theatrus/ledbrick/firmware/components/ledbrick_scheduler/ledbrick_scheduler.cpp

#include "ledbrick_scheduler.h"
#include "cJSON.h"
#include "esphome/core/log.h"
#include "esphome/core/application.h"
#include "esphome/components/light/light_state.h"
#include "esphome/components/number/number.h"
#include <algorithm>
#include <cmath>
#include <cstdlib>
#include <memory>

// The standalone implementations are compiled separately by ESPHome
// No need to include the .cpp files here

namespace esphome {
namespace ledbrick_scheduler {

static const char *const TAG = "ledbrick_scheduler";

void LEDBrickScheduler::setup() {
  ESP_LOGCONFIG(TAG, "Setting up LEDBrick Scheduler...");
  
  // Initialize the standalone scheduler
  scheduler_.set_num_channels(num_channels_);
  
  // Initialize the astronomical calculator with default location
  astro_calc_.set_location(latitude_, longitude_);
  astro_calc_.set_projection_settings(astronomical_projection_, time_shift_hours_, time_shift_minutes_);
  
  // Initialize persistent storage
  schedule_pref_ = global_preferences->make_preference<ScheduleStorage>(SCHEDULE_HASH);
  led_models_pref_ = global_preferences->make_preference<LedModelsStorage>(LED_MODELS_HASH);
  emergency_pref_ = global_preferences->make_preference<bool>(EMERGENCY_HASH);
  
  // Set up temperature hardware callbacks (moved from controller to hardware manager)
  temp_hardware_.set_fan_pwm_callback([this](float pwm) { this->on_fan_pwm_change(pwm); });
  temp_hardware_.set_fan_enable_callback([this](bool enabled) { this->on_fan_enable_change(enabled); });
  temp_hardware_.set_emergency_callback([this](bool emergency) { this->on_emergency_change(emergency); });
  
  // A thermal emergency survives a restart: keep the LEDs off until a reading confirms recovery.
  // Restore it before the schedule loads, so nothing turns the outputs on first.
  bool saved_emergency = false;
  if (emergency_pref_.load(&saved_emergency) && saved_emergency) {
    ESP_LOGW(TAG, "Thermal emergency was active before restart; LEDs stay off until temperatures recover");
    // Only the latch here: the fan component is not set up yet, so the first update()
    // sends the full-speed fan command once it can take effect
    ledbrick::TemperatureControlCommand command;
    command.emergency_state = true;
    command.override_normal_control = true;
    command.reason = "Thermal emergency restored after restart";
    temp_hardware_.apply_command(command, millis());
    temp_control_.update_hardware_state(temp_hardware_.get_hardware_state());
  }
  
  // Load schedule from flash storage (includes all settings in JSON). The custom LED
  // models come first, since channels name them.
  load_led_models_from_flash();
  load_schedule_from_flash();
  std::string model_error;
  if (!scheduler_.channels_have_models(&model_error)) {
    ESP_LOGE(TAG, "%s; using the standard LED for it until the model is posted to /api/led_models",
             model_error.c_str());
  }
  
  // Initialize temperature control
  temp_control_.set_config(temp_config_);
  
  // Enable temperature control unless the enable switch already restored a setting
  if (!temp_control_enable_requested_) {
    temp_control_.enable(true);
  }
  temp_control_initialized_ = true;
  
  // Try to get initial timezone from time source
  if (time_source_) {
    auto time = time_source_->now();
    if (time.is_valid()) {
      double detected_offset = static_cast<double>(time.timezone_offset()) / 3600.0;
      if (abs(detected_offset - timezone_offset_hours_) > 0.01) {
        ESP_LOGI(TAG, "Initial timezone offset detected: %.1fh (was %.1fh)", 
                 detected_offset, timezone_offset_hours_);
        timezone_offset_hours_ = detected_offset;
        astro_calc_.set_timezone_offset(timezone_offset_hours_);
      }
    }
  }
  
  // Load default astronomical schedule if no points exist
  if (scheduler_.is_schedule_empty()) {
    load_preset("default");
    if (flash_load_failed_) {
      // Run the default preset, but leave the saved copy alone rather than overwrite it at boot
      ESP_LOGE(TAG, "Saved schedule could not be loaded; running the default preset without saving it");
      save_pending_ = false;
    } else {
      ESP_LOGI(TAG, "No saved schedule found, loaded default preset");
      save_schedule_to_flash();  // Save the default schedule
    }
  }
  
  ESP_LOGI(TAG, "Schedule loaded - %zu points, %u channels, enabled: %s", 
           scheduler_.get_schedule_size(), num_channels_, enabled_ ? "true" : "false");
  
  // Update color sensors with initial values
  update_color_sensors();
  
  ESP_LOGCONFIG(TAG, "LEDBrick Scheduler setup complete");
  ESP_LOGCONFIG(TAG, "Temperature Control:");
  ESP_LOGCONFIG(TAG, "  Fan object: %s", fan_ ? "Connected" : "NOT CONNECTED");
  ESP_LOGCONFIG(TAG, "  Fan power switch: %s", fan_power_switch_ ? "Connected" : "NOT CONNECTED");
  ESP_LOGCONFIG(TAG, "  Temperature sensors: %zu", temp_sensors_.size());
  
  // Mark boot as complete and perform any deferred saves
  boot_complete_ = true;
  if (save_pending_) {
    ESP_LOGI(TAG, "Boot complete - performing deferred schedule save");
    save_pending_ = false;
    save_schedule_to_flash();
  }
}

void LEDBrickScheduler::update() {
  // ALWAYS check thermal emergency first, even if scheduler is disabled
  if (temp_hardware_.get_hardware_state().thermal_emergency) {
    // During thermal emergency, continuously force all outputs to zero
    // This prevents manual control from setting unsafe values
    for (uint8_t channel = 0; channel < num_channels_; channel++) {
      force_channel_output(channel, 0.0f, 0.0f);
    }
    // Skip to temperature control update
  } else if (!enabled_) {
    ESP_LOGV(TAG, "Scheduler disabled, skipping schedule update");
    // When scheduler is disabled but not in emergency, we don't change outputs
    // This allows manual control to work
  } else if (!has_valid_time()) {
    // Hold the outputs until the clock is set; the 00:00 values would be wrong
    uint32_t now = millis();
    if (last_time_warning_ms_ == 0 || now - last_time_warning_ms_ > 60000) {
      ESP_LOGW(TAG, "No valid time yet, holding channel outputs");
      last_time_warning_ms_ = now == 0 ? 1 : now;
    }
  } else {
    // Normal scheduler operation
    // Update timezone offset from time source if available
    update_timezone_from_time_source();
    
    // Update astronomical times for dynamic schedule points
    update_astronomical_times_for_scheduler();
    
    // Get current values from standalone scheduler and apply them. Interpolate to the
    // second so ramps move at every update instead of in one-minute steps
    uint16_t current_time = get_current_time_minutes();
    
    // Use astronomical interpolation if we have dynamic points
    auto values = scheduler_.get_values_at_seconds_with_astro(get_current_time_seconds(), scheduler_.get_astronomical_times());
    ESP_LOGD(TAG, "Scheduler values at %02d:%02d - valid: %s, channels: %zu, schedule_points: %zu", 
             current_time / 60, current_time % 60, 
             values.valid ? "true" : "false", 
             values.pwm_values.size(),
             scheduler_.get_schedule_size());
             
    // Check if moon simulation is active
    if (scheduler_.get_moon_simulation().enabled && values.valid && values.pwm_values.size() > 0) {
      // Get moon visibility status
      auto moon_times = get_moon_rise_set_times();
      bool moon_visible = (moon_times.rise_minutes < moon_times.set_minutes) ?
                         (current_time >= moon_times.rise_minutes && current_time <= moon_times.set_minutes) :
                         (current_time >= moon_times.rise_minutes || current_time <= moon_times.set_minutes);
      
      // Check if channels are dark
      bool all_dark = true;
      for (size_t i = 0; i < values.pwm_values.size(); i++) {
        if (values.pwm_values[i] > 0.1f) {
          all_dark = false;
          break;
        }
      }
      
      ESP_LOGD(TAG, "Moon sim status - Enabled: yes, Moon visible: %s, Channels dark: %s, Phase: %.1f%%, Ch1: PWM=%.1f%%, Current=%.3fA", 
               moon_visible ? "yes" : "no",
               all_dark ? "yes" : "no",
               get_moon_phase() * 100.0f,
               values.pwm_values[0], values.current_values[0]);
    }
    
    if (values.valid) {
      apply_values(values);
    } else {
      ESP_LOGW(TAG, "Scheduler returned invalid values at time %02d:%02d, schedule has %zu points", 
               current_time / 60, current_time % 60, scheduler_.get_schedule_size());
    }
  }
  
  // Update temperature control
  uint32_t current_millis = millis();
  if (temp_control_initialized_ && current_millis - last_temp_update_ >= 1000) {  // Update every second
    last_temp_update_ = current_millis;
    
    // Update temperature sensors
    update_temperature_sensors();
    
    // Update fan speed
    update_fan_speed();
    
    // Run temperature control update with new command-based interface
    auto command = temp_control_.compute_control_command(current_millis);
    temp_hardware_.apply_command(command, current_millis);
    temp_control_.update_hardware_state(temp_hardware_.get_hardware_state());
    
    // Publish sensor values periodically (every 5 seconds)
    if (current_millis - last_sensor_publish_ >= 5000) {
      publish_temp_sensor_values();
      last_sensor_publish_ = current_millis;
    }
  }
  
  // Log status every 10 seconds (reduce log spam)
  if (current_millis - last_log_time_ms_ > 10000) {
    if (temp_hardware_.get_hardware_state().thermal_emergency) {
      ESP_LOGD(TAG, "THERMAL EMERGENCY - All outputs forced to zero");
    } else if (!enabled_) {
      ESP_LOGD(TAG, "Scheduler disabled - manual control active");
    } else {
      uint16_t log_time = get_current_time_minutes();
      auto log_values = scheduler_.get_values_at_time_with_astro(log_time, scheduler_.get_astronomical_times());
      ESP_LOGD(TAG, "Scheduler active at %02u:%02u - Ch1: PWM=%.1f%%, Ch2: PWM=%.1f%%, Moon: %s", 
               log_time / 60, log_time % 60,
               log_values.pwm_values.size() > 0 ? log_values.pwm_values[0] : 0.0f,
               log_values.pwm_values.size() > 1 ? log_values.pwm_values[1] : 0.0f,
               scheduler_.get_moon_simulation().enabled ? "enabled" : "disabled");
      
      // Also log if we recently recovered from emergency
      bool current_emergency = temp_hardware_.get_hardware_state().thermal_emergency;
      if (was_emergency_ && !current_emergency) {
        recovery_time_ms_ = current_millis;
        ESP_LOGI(TAG, "Recently recovered from thermal emergency");
      }
      if (recovery_time_ms_ > 0 && current_millis - recovery_time_ms_ < 30000) {  // Log for 30 seconds after recovery
        ESP_LOGD(TAG, "Post-emergency recovery: %" PRIu32 " seconds ago", (current_millis - recovery_time_ms_) / 1000);
      }
      was_emergency_ = current_emergency;
    }
    last_log_time_ms_ = current_millis;
  }
}

void LEDBrickScheduler::dump_config() {
  ESP_LOGCONFIG(TAG, "LEDBrick Scheduler:");
  ESP_LOGCONFIG(TAG, "  Channels: %u", num_channels_);
  ESP_LOGCONFIG(TAG, "  Update Interval: %" PRIu32 " ms", this->get_update_interval());
  ESP_LOGCONFIG(TAG, "  Enabled: %s", enabled_ ? "YES" : "NO");
  ESP_LOGCONFIG(TAG, "  PWM Scale: %.2f (%.0f%%)", pwm_scale_, pwm_scale_ * 100.0f);
  ESP_LOGCONFIG(TAG, "  Timezone: %s (UTC%+.1fh)", timezone_.c_str(), timezone_offset_hours_);
  ESP_LOGCONFIG(TAG, "  Location: %.4f°N, %.4f°W", latitude_, -longitude_);
  ESP_LOGCONFIG(TAG, "  Schedule Points: %zu", scheduler_.get_schedule_size());
  ESP_LOGCONFIG(TAG, "  Time Source: %s", time_source_ ? "CONFIGURED" : "NOT SET");
  
  if (astronomical_projection_) {
    ESP_LOGCONFIG(TAG, "  Astronomical Projection: ENABLED");
    ESP_LOGCONFIG(TAG, "  Time Shift: %+dh %+dm", time_shift_hours_, time_shift_minutes_);
  } else {
    ESP_LOGCONFIG(TAG, "  Astronomical Projection: DISABLED");
  }
  
  if (time_source_) {
    uint16_t current_time = get_current_time_minutes();
    ESP_LOGCONFIG(TAG, "  Current Local Time: %02u:%02u (%u minutes)", 
                  current_time / 60, current_time % 60, current_time);
  }
  
  // Temperature control configuration
  ESP_LOGCONFIG(TAG, "Temperature Control:");
  ESP_LOGCONFIG(TAG, "  Target Temperature: %.1f°C", temp_config_.target_temp_c);
  ESP_LOGCONFIG(TAG, "  PID Parameters: Kp=%.2f, Ki=%.3f, Kd=%.2f", temp_config_.kp, temp_config_.ki, temp_config_.kd);
  ESP_LOGCONFIG(TAG, "  Fan PWM Range: %.1f%% - %.1f%%", temp_config_.min_fan_pwm, temp_config_.max_fan_pwm);
  ESP_LOGCONFIG(TAG, "  Emergency Temperature: %.1f°C", temp_config_.emergency_temp_c);
  ESP_LOGCONFIG(TAG, "  Temperature Sensors: %zu", temp_sensors_.size());
}

void LEDBrickScheduler::add_schedule_point(const SchedulePoint &point) {
  scheduler_.add_schedule_point(point);
  
  // Save to flash automatically
  save_schedule_to_flash();
  
  ESP_LOGD(TAG, "Added schedule point at %02u:%02u", 
           point.time_minutes / 60, point.time_minutes % 60);
}

void LEDBrickScheduler::set_schedule_point(uint16_t time_minutes, const std::vector<float> &pwm_values, 
                                          const std::vector<float> &current_values) {
  scheduler_.set_schedule_point(time_minutes, pwm_values, current_values);
  
  // Save to flash automatically
  save_schedule_to_flash();
}

void LEDBrickScheduler::add_dynamic_schedule_point(LEDScheduler::DynamicTimeType type, int16_t offset_minutes,
                                                  const std::vector<float> &pwm_values,
                                                  const std::vector<float> &current_values) {
  scheduler_.add_dynamic_schedule_point(type, offset_minutes, pwm_values, current_values);
  
  // Save to flash automatically
  save_schedule_to_flash();
  
  ESP_LOGD(TAG, "Added dynamic schedule point: %s %+d minutes", 
           LEDScheduler::dynamic_time_type_to_string(type).c_str(), offset_minutes);
}

void LEDBrickScheduler::remove_schedule_point(uint16_t time_minutes) {
  scheduler_.remove_schedule_point(time_minutes);
  
  // Save to flash automatically
  save_schedule_to_flash();
  
  ESP_LOGD(TAG, "Removed schedule point at %02u:%02u", time_minutes / 60, time_minutes % 60);
}

void LEDBrickScheduler::remove_dynamic_schedule_point(LEDScheduler::DynamicTimeType type, int16_t offset_minutes) {
  scheduler_.remove_dynamic_schedule_point(type, offset_minutes);
  
  // Save to flash automatically
  save_schedule_to_flash();
  
  ESP_LOGD(TAG, "Removed dynamic schedule point: %s %+d minutes", 
           LEDScheduler::dynamic_time_type_to_string(type).c_str(), offset_minutes);
}

void LEDBrickScheduler::clear_schedule() {
  scheduler_.clear_schedule();
  
  // Save to flash automatically
  save_schedule_to_flash();
  
  ESP_LOGD(TAG, "Cleared all schedule points");
}

bool LEDBrickScheduler::load_preset(const std::string &preset_name, bool save) {
  if (preset_name == "sunrise_sunset") {
    create_sunrise_sunset_preset_with_astro_data();
  } else if (!scheduler_.load_preset(preset_name)) {
    ESP_LOGW(TAG, "Unknown preset '%s'; schedule unchanged", preset_name.c_str());
    return false;
  }

  if (save) {
    save_schedule_to_flash();
  }

  ESP_LOGI(TAG, "Loaded preset '%s' with %zu points", preset_name.c_str(), scheduler_.get_schedule_size());
  return true;
}

void LEDBrickScheduler::save_preset(const std::string &preset_name) {
  scheduler_.save_preset(preset_name);
  ESP_LOGI(TAG, "Saved current schedule as preset '%s'", preset_name.c_str());
}

bool LEDBrickScheduler::has_valid_time() const {
  return time_source_ != nullptr && time_source_->now().is_valid();
}

uint16_t LEDBrickScheduler::get_current_time_minutes() const {
  if (!time_source_) {
    ESP_LOGW(TAG, "No time source configured");
    return 0;
  }
  
  auto time = time_source_->now();
  if (!time.is_valid()) {
    ESP_LOGW(TAG, "Time source not available");
    return 0;
  }
  
  return time.hour * 60 + time.minute;
}

uint32_t LEDBrickScheduler::get_current_time_seconds() const {
  if (!time_source_) {
    return 0;
  }
  auto time = time_source_->now();
  if (!time.is_valid()) {
    return 0;
  }
  return time.hour * 3600u + time.minute * 60u + time.second;
}

InterpolationResult LEDBrickScheduler::get_current_values() const {
  // Same interpolation as update(), so dynamic (sunrise-relative etc.) points count
  return scheduler_.get_values_at_seconds_with_astro(get_current_time_seconds(), scheduler_.get_astronomical_times());
}

float LEDBrickScheduler::get_led_temperature_c() const {
  // The emitter's sensors sit on the board near the LEDs' pads. Without a working one,
  // use the reference temperature, which leaves the output uncompensated.
  const auto &status = temp_control_.get_status();
  if (status.sensors_valid_count > 0 && std::isfinite(status.current_temp_c) && status.current_temp_c > 0.0f) {
    return status.current_temp_c;
  }
  return 25.0f;
}

float LEDBrickScheduler::get_channel_level(uint8_t channel) const {
  if (!scheduler_.is_curve_channel(channel) || channel >= last_levels_.size()) {
    return -1.0f;
  }
  return last_levels_[channel];
}

bool LEDBrickScheduler::set_channel_dimming(uint8_t channel, ledbrick::DimMode mode, ledbrick::DimPriority priority,
                                            float floor_current, const std::vector<ledbrick::LedGroup> &leds,
                                            std::string *error) {
  if (!scheduler_.set_channel_dimming(channel, mode, priority, floor_current, leds, error)) {
    return false;
  }
  ESP_LOGI(TAG, "Channel %u dimming: %s, %s first, floor %.3f A, %s LEDs", channel + 1,
           mode == ledbrick::DimMode::CURVE ? "curve" : "manual",
           priority == ledbrick::DimPriority::PWM_FIRST ? "PWM" : "current", floor_current,
           leds.empty() ? "default" : "custom");
  // Drive the channel the new way at the next update, without a transition
  force_next_update_ = true;
  return true;
}

bool LEDBrickScheduler::set_led_models_json(const std::string &json, std::string *error, bool *save_failed) {
  *save_failed = false;
  // A set too large for its record is refused before anything changes
  if (!scheduler_.import_led_models_json(json, error, sizeof(LedModelsStorage::json_data) - 1)) {
    return false;
  }
  ESP_LOGI(TAG, "Custom LED models: %zu", scheduler_.get_custom_led_models().size());
  // Curve channels pick up the new curves at the next update
  force_next_update_ = true;
  if (!save_led_models_to_flash()) {
    if (error) *error = "LED models applied but not saved; they will be lost on restart";
    *save_failed = true;
    return false;
  }
  return true;
}

bool LEDBrickScheduler::set_channel_manual_level(uint8_t channel, float level) {
  if (!scheduler_.is_curve_channel(channel)) {
    ESP_LOGW(TAG, "Manual level rejected - channel %u is not in curve mode", channel);
    return false;
  }
  level = std::max(0.0f, std::min(level, 1.0f));
  ledbrick::DriveLimits limits;
  limits.max_current_a = scheduler_.get_channel_max_current(channel);
  ledbrick::Drive drive = scheduler_.channel_dimmer(channel).drive_for_level(level, limits, get_led_temperature_c());
  if (!set_channel_manual_control(channel, drive.pwm * 100.0f, drive.current_a)) {
    return false;
  }
  if (last_levels_.size() != num_channels_) {
    last_levels_.assign(num_channels_, -1.0f);
  }
  last_levels_[channel] = level;
  return true;
}

InterpolationResult LEDBrickScheduler::get_actual_channel_values() const {
  InterpolationResult result;
  result.pwm_values.resize(num_channels_, 0.0f);
  result.current_values.resize(num_channels_, 0.0f);
  result.valid = true;
  
  // Get actual values from the ESPHome components
  for (uint8_t channel = 0; channel < num_channels_; channel++) {
    // Get PWM value from light entity
    auto light_it = lights_.find(channel);
    if (light_it != lights_.end() && light_it->second) {
      // Get actual current state (not the call values)
      auto remote_values = light_it->second->remote_values;
      // Check if light is on - if off, report 0% regardless of brightness setting
      if (remote_values.is_on()) {
        // Get brightness as percentage (0-100)
        result.pwm_values[channel] = remote_values.get_brightness() * 100.0f;
      } else {
        // Light is off, report 0%
        result.pwm_values[channel] = 0.0f;
      }
    }
    
    // Get current value from current control
    auto current_it = current_controls_.find(channel);
    if (current_it != current_controls_.end() && current_it->second) {
      result.current_values[channel] = current_it->second->state;
    }
  }
  
  return result;
}

void LEDBrickScheduler::set_enabled(bool enabled) {
  if (enabled_ == enabled) {
    return;  // No change, skip save
  }

  enabled_ = enabled;

  // The scheduler's flash JSON is the only persisted copy of this setting
  save_schedule_to_flash();
  ESP_LOGI(TAG, "Scheduler %s and saved", enabled ? "enabled" : "disabled");
}

bool LEDBrickScheduler::set_pwm_scale(float scale) {
  if (scale < 0.0f) {
    scale = 0.0f;
  } else if (scale > 1.0f) {
    scale = 1.0f;
  }

  bool saved = true;
  if (abs(pwm_scale_ - scale) > 0.001f) {
    pwm_scale_ = scale;
    ESP_LOGI(TAG, "PWM scale set to %.2f (%.0f%%)", pwm_scale_, pwm_scale_ * 100.0f);
    saved = save_schedule_to_flash();

    // Force immediate update to apply new scale
    update();
  }
  return saved;
}

void LEDBrickScheduler::create_sunrise_sunset_preset_with_astro_data() const {
  // Calculate actual sunrise and sunset times using astronomical calculator
  update_astro_calculator_settings();
  auto dt = esphome_time_to_datetime();
  auto sun_times = astro_calc_.get_projected_sun_rise_set_times(dt);
  
  // Use calculated times or fallback to defaults
  uint16_t sunrise_minutes = sun_times.rise_valid ? sun_times.rise_minutes : 420;  // Default 7:00 AM
  uint16_t sunset_minutes = sun_times.set_valid ? sun_times.set_minutes : 1080;    // Default 6:00 PM
  
  ESP_LOGI(TAG, "Creating astronomical sunrise/sunset preset: sunrise=%02u:%02u, sunset=%02u:%02u", 
           sunrise_minutes / 60, sunrise_minutes % 60,
           sunset_minutes / 60, sunset_minutes % 60);
  
  // Use the standalone scheduler to create the default astronomical preset
  // Note: The new default preset is dynamic and doesn't use specific sunrise/sunset times
  const_cast<LEDScheduler&>(scheduler_).create_default_astronomical_preset();
}

void LEDBrickScheduler::apply_values(const InterpolationResult &values) {
  ESP_LOGD(TAG, "apply_values called - num_channels: %u, values_size: %zu, first_pwm: %.1f%%", 
           num_channels_, values.pwm_values.size(), 
           values.pwm_values.empty() ? 0.0f : values.pwm_values[0]);
  
  const float led_temp = get_led_temperature_c();
  for (uint8_t channel = 0; channel < num_channels_; channel++) {
    if (channel >= values.pwm_values.size() || channel >= values.current_values.size()) {
      ESP_LOGW(TAG, "Schedule has %zu channels, expected %u", values.pwm_values.size(), num_channels_);
      break;
    }

    auto current_it = current_controls_.find(channel);
    auto max_current_it = max_current_controls_.find(channel);
    float max_current = scheduler_.get_channel_max_current(channel);
    if (max_current_it != max_current_controls_.end() && max_current_it->second) {
      max_current = max_current_it->second->state;
    }

    // Manual channels: the schedule sets the PWM and current. Curve channels: it sets a
    // level, and the channel's LED curves give the current and PWM for it at the LEDs'
    // temperature.
    float target_current;
    float brightness;
    uint32_t transition_ms = force_next_update_ ? 0 : 1000;
    const bool curve = scheduler_.is_curve_channel(channel);
    if (curve) {
      float level = std::max(0.0f, std::min(values.pwm_values[channel] * pwm_scale_ / 100.0f, 1.0f));
      ledbrick::DriveLimits limits;
      limits.max_current_a = max_current;
      ledbrick::Drive drive = scheduler_.channel_dimmer(channel).drive_for_level(level, limits, led_temp);
      target_current = drive.current_a;
      brightness = drive.pwm;
      if (last_levels_.size() != num_channels_) {
        last_levels_.assign(num_channels_, -1.0f);
      }
      last_levels_[channel] = level;
      // Current and PWM change together; a PWM transition would lag behind the current
      transition_ms = 0;
    } else {
      target_current = std::min(values.current_values[channel], max_current);
      brightness = values.pwm_values[channel] * pwm_scale_ / 100.0f;
      if (channel < last_levels_.size()) {
        last_levels_[channel] = -1.0f;
      }
    }

    // Apply current control with limiting
    // We need to do this before applying PWM to ensure LED controller enters the right state
    if (current_it != current_controls_.end() && current_it->second) {

      // Always update regardless of whether value has changed
      // Set the current control value
      current_it->second->publish_state(target_current);
      
      if (last_current_values_.size() <= channel) {
        last_current_values_.resize(num_channels_, -1.0f);
      }
      last_current_values_[channel] = target_current;
      
      // Enhanced logging for channel 1 when values change
      if (channel == 0) {
        ESP_LOGD(TAG, "Ch1 current update: %.3fA (input: %.3fA, max limit: %.3fA, was: %.3fA)", 
                 target_current, values.current_values[channel],
                 max_current_it != max_current_controls_.end() && max_current_it->second ? 
                 max_current_it->second->state : 999.0f,
                 last_current_values_.size() > channel ? last_current_values_[channel] : -1.0f);
      }
      
      ESP_LOGV(TAG, "Updated current %u to %.3fA (limited from %.3fA)", 
               channel, target_current, values.current_values[channel]);
    } else {
      ESP_LOGVV(TAG, "No current control found for channel %u", channel);
    }

    // Apply PWM to light entity
    auto light_it = lights_.find(channel);
    if (light_it != lights_.end() && light_it->second) {
      float scaled_pwm = brightness * 100.0f;

      // Always update regardless of whether value has changed
      ESP_LOGD(TAG, "Updating light %u: scaled_pwm=%.2f%%, brightness=%.3f (was %.3f)%s",
               channel, scaled_pwm, brightness,
               (last_pwm_values_.size() > channel) ? last_pwm_values_[channel] : -1.0f,
               curve ? " [curve]" : "");

      // Create light call to set brightness. Curve channels dim below 0.1% with PWM, so
      // any duty the dimmer gives turns them on.
      bool on = curve ? brightness > 0.0f : brightness > 0.001f;
      auto call = light_it->second->make_call();
      call.set_state(on);
      if (on) {
        call.set_brightness(brightness);
      }
      // Manual channels ease over 1 s; curve channels and forced updates change at once
      call.set_transition_length(transition_ms);
      call.perform();
      
      ESP_LOGV(TAG, "Light %u call performed", channel);
      
      if (last_pwm_values_.size() <= channel) {
        last_pwm_values_.resize(num_channels_, -1.0f);
      }
      last_pwm_values_[channel] = brightness;
      
      ESP_LOGV(TAG, "Updated light %u brightness to %.3f (%.1f%% * %.2f scale = %.1f%%)", 
               channel, brightness, values.pwm_values[channel], pwm_scale_, scaled_pwm);
    } else {
      ESP_LOGVV(TAG, "No light entity found for channel %u", channel);
    }
    
  }
  
  // Clear force update flag after applying all values
  if (force_next_update_) {
    ESP_LOGD(TAG, "Force update completed - clearing flag");
    force_next_update_ = false;
  }
}


void LEDBrickScheduler::add_light(uint8_t channel, light::LightState *light) {
  lights_[channel] = light;
  ESP_LOGD(TAG, "Added light entity for channel %u", channel);
}

void LEDBrickScheduler::add_current_control(uint8_t channel, number::Number *control) {
  current_controls_[channel] = control;
  ESP_LOGD(TAG, "Added current control for channel %u", channel);
}

void LEDBrickScheduler::add_max_current_control(uint8_t channel, number::Number *control) {
  max_current_controls_[channel] = control;
  ESP_LOGD(TAG, "Added max current control for channel %u", channel);
}



bool LEDBrickScheduler::save_schedule_to_flash() {
  // Prevent saving during boot to avoid race conditions
  if (!boot_complete_) {
    save_pending_ = true;
    ESP_LOGD(TAG, "Boot in progress - deferring schedule save");
    return true;
  }
  
  // Export the complete schedule as JSON (includes moon settings, channel configs, etc.)
  std::string json_output;
  export_schedule_json(json_output, true);
  
  // Allocate storage on heap to avoid stack overflow
  std::unique_ptr<ScheduleStorage> storage(new (std::nothrow) ScheduleStorage);
  if (!storage) {
    ESP_LOGE(TAG, "Failed to allocate memory for schedule storage");
    return false;
  }
  
  // A truncated document cannot be parsed at the next boot, so keep the previous copy instead
  if (json_output.length() >= sizeof(storage->json_data)) {
    ESP_LOGE(TAG, "Schedule JSON too large to save (%zu bytes, limit %zu); keeping previous copy",
             json_output.length(), sizeof(storage->json_data) - 1);
    return false;
  }
  
  memset(storage.get(), 0, sizeof(ScheduleStorage));
  
  storage->version = 2;  // Version 2 uses JSON format
  storage->json_length = static_cast<uint32_t>(json_output.length());
  
  // Copy JSON data
  std::memcpy(storage->json_data, json_output.c_str(), storage->json_length);
  storage->json_data[storage->json_length] = '\0';  // Null terminate
  
  bool success = schedule_pref_.save(storage.get());
  if (success) {
    flash_load_failed_ = false;  // The stored copy is valid again
    ESP_LOGD(TAG, "Saved schedule to flash (JSON format, %" PRIu32 " bytes)", storage->json_length);
    // ESPHome holds preference writes for up to a minute, so a power cut soon after a change
    // lost it although the change had been reported saved. Write it out a quarter second
    // after the last save; a burst of saves (one per channel, say) is written once.
    this->set_timeout("flush_settings", 250, []() { global_preferences->sync(); });
  } else {
    ESP_LOGW(TAG, "Failed to save schedule to flash");
  }
  return success;
}

bool LEDBrickScheduler::save_led_models_to_flash() {
  std::string json = scheduler_.export_led_models_json(true);
  std::unique_ptr<LedModelsStorage> storage(new (std::nothrow) LedModelsStorage);
  if (!storage) {
    ESP_LOGE(TAG, "Failed to allocate memory for LED model storage");
    return false;
  }
  if (json.length() >= sizeof(storage->json_data)) {
    ESP_LOGE(TAG, "LED models too large to save (%zu bytes, limit %zu)", json.length(),
             sizeof(storage->json_data) - 1);
    return false;
  }
  memset(storage.get(), 0, sizeof(LedModelsStorage));
  storage->version = 1;
  storage->json_length = static_cast<uint32_t>(json.length());
  std::memcpy(storage->json_data, json.c_str(), storage->json_length);

  if (!led_models_pref_.save(storage.get())) {
    ESP_LOGW(TAG, "Failed to save LED models to flash");
    return false;
  }
  ESP_LOGD(TAG, "Saved LED models to flash (%" PRIu32 " bytes)", storage->json_length);
  // Shares the schedule's flush, so changes to both are written together
  this->set_timeout("flush_settings", 250, []() { global_preferences->sync(); });
  return true;
}

void LEDBrickScheduler::load_led_models_from_flash() {
  std::unique_ptr<LedModelsStorage> storage(new (std::nothrow) LedModelsStorage);
  if (!storage) {
    ESP_LOGE(TAG, "Failed to allocate memory for LED model storage");
    return;
  }
  if (!led_models_pref_.load(storage.get())) {
    ESP_LOGD(TAG, "No custom LED models in flash");
    return;
  }
  if (storage->version != 1 || storage->json_length >= sizeof(storage->json_data)) {
    ESP_LOGW(TAG, "Saved LED models have version %" PRIu32 ", length %" PRIu32 "; ignoring them",
             storage->version, storage->json_length);
    return;
  }
  std::string error;
  if (scheduler_.import_led_models_json(std::string(storage->json_data, storage->json_length), &error)) {
    ESP_LOGI(TAG, "Loaded %zu custom LED models", scheduler_.get_custom_led_models().size());
  } else {
    ESP_LOGE(TAG, "Saved LED models could not be loaded: %s", error.c_str());
  }
}

void LEDBrickScheduler::load_schedule_from_flash() {
  // Allocate storage on heap to avoid stack overflow
  std::unique_ptr<ScheduleStorage> storage(new (std::nothrow) ScheduleStorage);
  if (!storage) {
    ESP_LOGE(TAG, "Failed to allocate memory for schedule storage");
    return;
  }
  
  bool loaded = schedule_pref_.load(storage.get());
  if (!loaded) {
    ESP_LOGD(TAG, "No saved schedule found in flash");
    return;
  }
  
  // Check version
  if (storage->version == 2) {
    // Version 2: JSON format
    if (storage->json_length > 0 && storage->json_length < sizeof(storage->json_data)) {
      storage->json_data[storage->json_length] = '\0';  // Ensure null terminated
      std::string json_input(storage->json_data);
      
      ESP_LOGD(TAG, "Loading schedule from flash (JSON format, %" PRIu32 " bytes)", storage->json_length);
      
      std::string error;
      if (import_schedule_json(json_input, &error, true)) {
        ESP_LOGI(TAG, "Successfully loaded schedule from flash (JSON format)");
        ESP_LOGI(TAG, "Loaded: %zu points, Moon: %s, Location: %.4f,%.4f", 
                 scheduler_.get_schedule_size(),
                 scheduler_.get_moon_simulation().enabled ? "ON" : "OFF",
                 latitude_, longitude_);
      } else {
        ESP_LOGW(TAG, "Failed to import schedule JSON from flash: %s", error.c_str());
        flash_load_failed_ = true;
      }
    } else {
      ESP_LOGW(TAG, "Saved schedule has invalid length %" PRIu32, storage->json_length);
      flash_load_failed_ = true;
    }
  } else if (storage->version == 0 || storage->version == 1) {
    // Legacy format - try to migrate
    ESP_LOGW(TAG, "Found legacy schedule format in flash, migration not supported");
  } else {
    ESP_LOGW(TAG, "Unknown schedule storage version %" PRIu32, storage->version);
    flash_load_failed_ = true;
  }
  // unique_ptr automatically deletes
}

void LEDBrickScheduler::export_schedule_json(std::string &json_output, bool for_storage) const {
  if (for_storage) {
    // Compact form for flash; dynamic point times are recomputed after loading
    json_output = scheduler_.export_json_minified();
  } else if (astronomical_projection_) {
    // If astronomical projection is enabled, we need to update the scheduler's
    // astronomical times with projected values before exporting
    // Get projected sun times (with time shift applied)
    auto projected_sun_times = get_daily_astro_times_().projected_sun;
    
    // Calculate solar noon from projected times
    uint16_t solar_noon = 720;  // Default to noon
    if (projected_sun_times.rise_valid && projected_sun_times.set_valid) {
      // Handle case where sunset happens after midnight
      int rise_mins = static_cast<int>(projected_sun_times.rise_minutes);
      int set_mins = static_cast<int>(projected_sun_times.set_minutes);
      
      // If sunset is before sunrise, it means sunset is on the next day
      if (set_mins < rise_mins) {
        set_mins += 1440;  // Add 24 hours
      }
      
      solar_noon = (rise_mins + set_mins) / 2;
      
      // Wrap back to 0-1439 range
      while (solar_noon >= 1440) {
        solar_noon -= 1440;
      }
    }
    
    // Calculate civil twilight times
    uint16_t civil_dawn = projected_sun_times.rise_valid ? 
      (projected_sun_times.rise_minutes > 30 ? projected_sun_times.rise_minutes - 30 : 0) : 390;
    uint16_t civil_dusk = projected_sun_times.set_valid ? 
      (projected_sun_times.set_minutes < 1410 ? projected_sun_times.set_minutes + 30 : 1439) : 1110;
    
    // Build projected astronomical times
    LEDScheduler::AstronomicalTimes projected_times;
    projected_times.sunrise_minutes = projected_sun_times.rise_valid ? projected_sun_times.rise_minutes : 420;
    projected_times.sunset_minutes = projected_sun_times.set_valid ? projected_sun_times.set_minutes : 1080;
    projected_times.solar_noon_minutes = solar_noon;
    projected_times.civil_dawn_minutes = civil_dawn;
    projected_times.civil_dusk_minutes = civil_dusk;
    projected_times.nautical_dawn_minutes = civil_dawn > 30 ? civil_dawn - 30 : 0;
    projected_times.nautical_dusk_minutes = civil_dusk < 1410 ? civil_dusk + 30 : 1439;
    projected_times.astronomical_dawn_minutes = civil_dawn > 60 ? civil_dawn - 60 : 0;
    projected_times.astronomical_dusk_minutes = civil_dusk < 1380 ? civil_dusk + 60 : 1439;
    projected_times.valid = true;
    
    // Get current astronomical times before modification
    LEDScheduler::AstronomicalTimes original_times = scheduler_.get_astronomical_times();
    
    // Temporarily set projected times for export
    const_cast<LEDScheduler&>(scheduler_).set_astronomical_times(projected_times);
    
    // Export with projected times
    json_output = scheduler_.export_json();
    
    // Restore original astronomical times to prevent moon simulation corruption
    const_cast<LEDScheduler&>(scheduler_).set_astronomical_times(original_times);
  } else {
    // Use normal export without projection
    json_output = scheduler_.export_json();
  }
  
  // Parse and modify the JSON to add ESPHome-specific fields
  // For simplicity, we'll create a new JSON string
  size_t closing_brace = json_output.rfind('}');
  if (closing_brace != std::string::npos) {
    // Add temperature control configuration
    std::string temp_config_json = temp_control_.export_config_json();
    
    // The current time changes every minute; leaving it out of the stored copy
    // avoids rewriting flash when nothing else changed
    std::string current_time_field;
    if (!for_storage) {
      current_time_field = ",\"current_time_minutes\":" + std::to_string(get_current_time_minutes());
    }
    
    json_output.insert(closing_brace, 
      ",\"timezone\":\"" + timezone_ + 
      "\",\"timezone_offset_hours\":" + std::to_string(timezone_offset_hours_) +
      current_time_field +
      ",\"enabled\":" + std::string(enabled_ ? "true" : "false") +
      (for_storage ? ",\"pwm_scale\":" + std::to_string(pwm_scale_) : std::string()) +
      ",\"latitude\":" + std::to_string(latitude_) +
      ",\"longitude\":" + std::to_string(longitude_) +
      ",\"astronomical_projection\":" + std::string(astronomical_projection_ ? "true" : "false") +
      ",\"time_shift_hours\":" + std::to_string(time_shift_hours_) +
      ",\"time_shift_minutes\":" + std::to_string(time_shift_minutes_) +
      ",\"temperature_control\":" + temp_config_json);
  }
}

bool LEDBrickScheduler::import_schedule_json(const std::string &json_input, std::string *error, bool from_flash) {
  ESP_LOGI(TAG, "Importing schedule from JSON (%zu chars)", json_input.length());
  
  auto fail = [error](const std::string &message) {
    ESP_LOGW(TAG, "Schedule import rejected: %s", message.c_str());
    if (error) *error = message;
    return false;
  };
  
  cJSON *root = cJSON_Parse(json_input.c_str());
  if (root == nullptr || !cJSON_IsObject(root)) {
    cJSON_Delete(root);
    return fail("invalid JSON");
  }
  
  // The firmware drives a fixed number of outputs; a schedule for another count
  // would leave channels without values
  cJSON *channels_item = cJSON_GetObjectItemCaseSensitive(root, "num_channels");
  if (cJSON_IsNumber(channels_item) && channels_item->valuedouble != num_channels_) {
    cJSON_Delete(root);
    return fail("num_channels must be " + std::to_string(num_channels_));
  }
  
  // Read the settings fields. A bad field rejects an API request; in a schedule
  // loaded from flash it is skipped so the rest of the saved schedule still loads.
  std::string field_error;
  auto bad_field = [&](const char *key) {
    if (field_error.empty()) field_error = std::string(key) + " is missing a valid value";
  };
  auto read_bool = [&](const char *key, bool &out, bool &present) {
    cJSON *item = cJSON_GetObjectItemCaseSensitive(root, key);
    if (item == nullptr) return;
    if (!cJSON_IsBool(item)) { bad_field(key); return; }
    out = cJSON_IsTrue(item);
    present = true;
  };
  auto read_number = [&](const char *key, double low, double high, double &out, bool &present) {
    cJSON *item = cJSON_GetObjectItemCaseSensitive(root, key);
    if (item == nullptr) return;
    if (!cJSON_IsNumber(item) || !(item->valuedouble >= low && item->valuedouble <= high)) { bad_field(key); return; }
    out = item->valuedouble;
    present = true;
  };
  
  bool new_enabled = enabled_, has_enabled = false;
  bool new_projection = astronomical_projection_, has_projection = false;
  double new_lat = latitude_, new_lon = longitude_, new_tz = timezone_offset_hours_;
  double new_shift_h = time_shift_hours_, new_shift_m = time_shift_minutes_, new_pwm_scale = pwm_scale_;
  bool has_lat = false, has_lon = false, has_tz = false, has_shift_h = false, has_shift_m = false, has_pwm_scale = false;
  read_bool("enabled", new_enabled, has_enabled);
  read_bool("astronomical_projection", new_projection, has_projection);
  read_number("latitude", -90.0, 90.0, new_lat, has_lat);
  read_number("longitude", -180.0, 180.0, new_lon, has_lon);
  // Older firmware exported negative offsets wrapped by a day (17 for UTC-7), so its exports
  // were rejected here. The clock replaces this value once it is set, so unwrap it, and skip
  // one that is still out of range, rather than reject the whole schedule
  cJSON *tz_item = cJSON_GetObjectItemCaseSensitive(root, "timezone_offset_hours");
  if (cJSON_IsNumber(tz_item)) {
    double tz = tz_item->valuedouble;
    if (tz > 14.0 && tz < 24.0) tz -= 24.0;
    if (tz >= -14.0 && tz <= 14.0) {
      new_tz = tz;
      has_tz = true;
    } else {
      ESP_LOGW(TAG, "Ignoring timezone_offset_hours %.2f; the clock sets it", tz_item->valuedouble);
    }
  } else if (tz_item != nullptr) {
    bad_field("timezone_offset_hours");
  }
  read_number("time_shift_hours", -12.0, 12.0, new_shift_h, has_shift_h);
  read_number("time_shift_minutes", -59.0, 59.0, new_shift_m, has_shift_m);
  // Only the flash copy carries pwm_scale; the web UI posts back a schedule it loaded
  // earlier, which would undo a later brightness change
  if (from_flash) {
    read_number("pwm_scale", 0.0, 1.0, new_pwm_scale, has_pwm_scale);
  }
  
  // Check the temperature control settings on a scratch controller first
  std::string temp_config_json;
  cJSON *temp_item = cJSON_GetObjectItemCaseSensitive(root, "temperature_control");
  if (temp_item != nullptr) {
    char *printed = cJSON_IsObject(temp_item) ? cJSON_PrintUnformatted(temp_item) : nullptr;
    if (printed != nullptr) {
      temp_config_json = printed;
      cJSON_free(printed);
      ledbrick::TemperatureControl scratch;
      scratch.set_config(temp_control_.get_config());
      std::string temp_error;
      // Settings saved by older firmware may be out of today's ranges; repair them on load
      if (!scratch.import_config_json(temp_config_json, &temp_error, from_flash)) {
        if (field_error.empty()) field_error = "temperature_control: " + temp_error;
        temp_config_json.clear();
      }
    } else if (field_error.empty()) {
      field_error = "temperature_control must be an object";
    }
  }
  cJSON_Delete(root);
  
  if (!field_error.empty()) {
    if (!from_flash) {
      return fail(field_error);
    }
    ESP_LOGW(TAG, "Saved schedule: %s; keeping the current value", field_error.c_str());
  }
  
  // The standalone import replaces the schedule only when it succeeds
  std::string import_error;
  // A saved channel naming a lost LED model keeps its schedule; the model can be posted again
  if (!scheduler_.import_json(json_input, &import_error, from_flash)) {
    return fail(import_error.empty() ? "schedule_points missing or invalid" : import_error);
  }
  
  // Apply the settings now that the whole document is accepted
  if (has_enabled) enabled_ = new_enabled;
  if (has_projection) astronomical_projection_ = new_projection;
  if (has_lat) latitude_ = new_lat;
  if (has_lon) longitude_ = new_lon;
  if (has_tz) timezone_offset_hours_ = new_tz;
  if (has_shift_h) time_shift_hours_ = static_cast<int>(new_shift_h);
  if (has_shift_m) time_shift_minutes_ = static_cast<int>(new_shift_m);
  if (has_pwm_scale) pwm_scale_ = static_cast<float>(new_pwm_scale);
  if (!temp_config_json.empty()) {
    // Saved settings always load (a latch restored at boot must not swap them for defaults)
    if (is_thermal_emergency() && !from_flash) {
      // New limits could clear the latched emergency without a real recovery
      ESP_LOGW(TAG, "Thermal emergency active; keeping current temperature control settings");
    } else {
      temp_control_.import_config_json(temp_config_json, nullptr, from_flash);
      temp_config_ = temp_control_.get_config();
      ESP_LOGI(TAG, "Imported temperature control configuration");
    }
  }
  
  // Update astronomical calculator with loaded settings (without saving during import)
  astro_calc_.set_location(latitude_, longitude_);
  astro_calc_.set_timezone_offset(timezone_offset_hours_);
  astro_calc_.set_projection_settings(astronomical_projection_, time_shift_hours_, time_shift_minutes_);
  
  // Don't save after import - callers decide; the flash load must not write back
  ESP_LOGI(TAG, "Successfully imported %zu schedule points, enabled=%s", 
           scheduler_.get_schedule_size(), enabled_ ? "true" : "false");
  ESP_LOGI(TAG, "Location: %.4f, %.4f; Time shift: %s %+d:%02d",
           latitude_, longitude_, 
           astronomical_projection_ ? "enabled" : "disabled",
           time_shift_hours_, abs(time_shift_minutes_));
  
  // Update max current controls from imported channel configs, within each number's range
  for (uint8_t ch = 0; ch < num_channels_; ch++) {
    auto max_current_it = max_current_controls_.find(ch);
    if (max_current_it != max_current_controls_.end() && max_current_it->second) {
      float max_current = std::min(scheduler_.get_channel_max_current(ch),
                                   max_current_it->second->traits.get_max_value());
      scheduler_.set_channel_max_current(ch, max_current);
      max_current_it->second->publish_state(max_current);
      ESP_LOGD(TAG, "Updated channel %u max current to %.2fA", ch, max_current);
    }
  }
  
  // Force update to refresh text sensors and color sensors
  update();
  update_color_sensors();
  
  ESP_LOGI(TAG, "Channel configurations updated: Ch0 color=%s", 
           scheduler_.get_channel_color(0).c_str());
  
  return true;
}


float LEDBrickScheduler::get_moon_phase() const {
  update_astro_calculator_settings();
  auto dt = esphome_time_to_datetime();
  return astro_calc_.get_moon_phase(dt);
}

float LEDBrickScheduler::get_moon_illumination() const {
  return AstronomicalCalculator::moon_illumination_from_phase(get_moon_phase());
}

const LEDBrickScheduler::DailyAstroTimes &LEDBrickScheduler::get_daily_astro_times_() const {
  // The moon search alone takes hundreds of double-precision steps, which the ESP32-S3 does
  // in software; the results only change with the date and settings, so keep them per day
  auto dt = esphome_time_to_datetime();
  DailyAstroTimes &cache = daily_astro_;
  if (cache.valid && cache.year == dt.year && cache.month == dt.month && cache.day == dt.day &&
      cache.latitude == latitude_ && cache.longitude == longitude_ &&
      cache.timezone_offset == timezone_offset_hours_ && cache.projection == astronomical_projection_ &&
      cache.shift_hours == time_shift_hours_ && cache.shift_minutes == time_shift_minutes_) {
    return cache;
  }
  
  update_astro_calculator_settings();
  cache.sun = astro_calc_.get_sun_rise_set_times(dt);
  cache.moon = astro_calc_.get_moon_rise_set_times(dt);
  // The projected versions return the real times when projection is off
  cache.projected_sun = astro_calc_.get_projected_sun_rise_set_times(dt);
  cache.projected_moon = astro_calc_.get_projected_moon_rise_set_times(dt);
  cache.year = dt.year;
  cache.month = dt.month;
  cache.day = dt.day;
  cache.latitude = latitude_;
  cache.longitude = longitude_;
  cache.timezone_offset = timezone_offset_hours_;
  cache.projection = astronomical_projection_;
  cache.shift_hours = time_shift_hours_;
  cache.shift_minutes = time_shift_minutes_;
  cache.valid = true;
  return cache;
}

AstronomicalCalculator::MoonTimes LEDBrickScheduler::get_moon_rise_set_times() const {
  // Use projected times if projection is enabled
  return get_daily_astro_times_().projected_moon;
}

AstronomicalCalculator::SunTimes LEDBrickScheduler::get_sun_rise_set_times() const {
  return get_daily_astro_times_().sun;
}

AstronomicalCalculator::SunTimes LEDBrickScheduler::get_projected_sun_rise_set_times() const {
  return get_daily_astro_times_().projected_sun;
}



float LEDBrickScheduler::get_moon_intensity() const {
  update_astro_calculator_settings();
  auto dt = esphome_time_to_datetime();
  return astro_calc_.get_moon_intensity(dt);
}

float LEDBrickScheduler::get_sun_intensity() const {
  update_astro_calculator_settings();
  auto dt = esphome_time_to_datetime();
  return astro_calc_.get_sun_intensity(dt);
}


float LEDBrickScheduler::get_projected_sun_intensity() const {
  update_astro_calculator_settings();
  auto dt = esphome_time_to_datetime();
  return astro_calc_.get_projected_sun_intensity(dt);
}

float LEDBrickScheduler::get_projected_moon_intensity() const {
  update_astro_calculator_settings();
  auto dt = esphome_time_to_datetime();
  return astro_calc_.get_projected_moon_intensity(dt);
}

AstronomicalCalculator::DateTime LEDBrickScheduler::esphome_time_to_datetime() const {
  if (!time_source_) {
    // Return a default time if no time source
    return AstronomicalCalculator::DateTime(2025, 1, 8, 12, 0, 0);
  }
  
  auto time = time_source_->now();
  if (!time.is_valid()) {
    // Return a default time if invalid
    return AstronomicalCalculator::DateTime(2025, 1, 8, 12, 0, 0);
  }
  
  // Return local time - the astronomical calculator will handle it correctly
  // The calculator returns rise/set times as minutes from midnight in local time
  return AstronomicalCalculator::DateTime(
    time.year, time.month, time.day_of_month, 
    time.hour, time.minute, time.second
  );
}

void LEDBrickScheduler::update_astro_calculator_settings() const {
  // Update location, timezone, and projection settings in the calculator
  astro_calc_.set_location(latitude_, longitude_);
  astro_calc_.set_timezone_offset(timezone_offset_hours_);
  astro_calc_.set_projection_settings(astronomical_projection_, time_shift_hours_, time_shift_minutes_);
}

void LEDBrickScheduler::update_timezone_from_time_source() {
  uint32_t current_millis = millis();
  
  // Only check every 60 seconds to reduce overhead
  if (current_millis - last_tz_update_ms_ < 60000 && last_tz_update_ms_ != 0) {
    return;
  }
  
  last_tz_update_ms_ = current_millis;
  
  if (!time_source_) {
    return;
  }
  
  auto time = time_source_->now();
  if (!time.is_valid()) {
    return;
  }
  
  // ESPHome's ESPTime struct has a UTC offset in seconds
  // Convert to hours for our astronomical calculator
  double new_timezone_offset = static_cast<double>(time.timezone_offset()) / 3600.0;
  
  // Check if timezone offset has changed
  if (abs(new_timezone_offset - timezone_offset_hours_) > 0.01) {
    ESP_LOGI(TAG, "Timezone offset updated from %.1fh to %.1fh", 
             timezone_offset_hours_, new_timezone_offset);
    timezone_offset_hours_ = new_timezone_offset;
    
    // Update the astronomical calculator with new timezone
    astro_calc_.set_timezone_offset(timezone_offset_hours_);
    
    // Force recalculation of astronomical times
    update_astronomical_times_for_scheduler();
    
    // Save the new timezone offset, unless that would overwrite a saved schedule
    // that failed to load (only a user change replaces it)
    if (!flash_load_failed_) {
      save_schedule_to_flash();
    }
  }
}

void LEDBrickScheduler::set_location(double latitude, double longitude) {
  // Check if location actually changed
  if (abs(latitude_ - latitude) < 0.0001 && abs(longitude_ - longitude) < 0.0001) {
    return;  // No change, skip save
  }
  
  latitude_ = latitude;
  longitude_ = longitude;
  
  // Update astronomical calculator
  astro_calc_.set_location(latitude_, longitude_);
  
  // Force immediate recalculation of astronomical times for dynamic schedule points
  update_astronomical_times_for_scheduler(true);
  
  // Force next update to re-evaluate schedule with new astronomical times
  force_next_update_ = true;
  
  // Save complete schedule (includes all settings)
  save_schedule_to_flash();
  ESP_LOGI(TAG, "Location updated to %.4f, %.4f and saved", latitude, longitude);
}

void LEDBrickScheduler::set_astronomical_projection(bool enabled) {
  // Check if value actually changed
  if (astronomical_projection_ == enabled) {
    return;  // No change, skip save
  }
  
  astronomical_projection_ = enabled;
  astro_calc_.set_projection_settings(astronomical_projection_, time_shift_hours_, time_shift_minutes_);
  
  // Force immediate recalculation of astronomical times for dynamic schedule points
  update_astronomical_times_for_scheduler(true);
  
  // Force next update to re-evaluate schedule with new astronomical times
  force_next_update_ = true;
  
  // Save complete schedule (includes all settings)
  save_schedule_to_flash();
  ESP_LOGI(TAG, "Astronomical projection %s and saved", enabled ? "enabled" : "disabled");
}

void LEDBrickScheduler::set_time_shift(int hours, int minutes) {
  // Check if values actually changed
  if (time_shift_hours_ == hours && time_shift_minutes_ == minutes) {
    return;  // No change, skip save
  }
  
  time_shift_hours_ = hours;
  time_shift_minutes_ = minutes;
  astro_calc_.set_projection_settings(astronomical_projection_, time_shift_hours_, time_shift_minutes_);
  
  // Force immediate recalculation of astronomical times for dynamic schedule points
  update_astronomical_times_for_scheduler(true);
  
  // Force next update to re-evaluate schedule with new astronomical times
  force_next_update_ = true;
  
  // Save to persistent storage (scheduler JSON)
  save_schedule_to_flash();
  ESP_LOGI(TAG, "Time shift updated to %+d:%02d and saved", hours, abs(minutes));
}

void LEDBrickScheduler::set_channel_config(uint8_t channel, const LEDScheduler::ChannelConfig& config) {
  // The standalone scheduler clamps max_current to the hardware limit
  scheduler_.set_channel_config(channel, config);
  
  // Keep the max-current number in step, within its own range
  auto max_current_it = max_current_controls_.find(channel);
  if (max_current_it != max_current_controls_.end() && max_current_it->second) {
    float max_current = std::min(scheduler_.get_channel_max_current(channel),
                                 max_current_it->second->traits.get_max_value());
    scheduler_.set_channel_max_current(channel, max_current);
    max_current_it->second->publish_state(max_current);
  }
}

void LEDBrickScheduler::set_channel_color(uint8_t channel, const std::string& rgb_hex) {
  // Check if value actually changed
  std::string current_color = scheduler_.get_channel_color(channel);
  if (current_color == rgb_hex) {
    return;  // No change, skip save
  }
  
  scheduler_.set_channel_color(channel, rgb_hex);
  
  // Update the color text sensor for this channel
  auto color_sensor_it = color_text_sensors_.find(channel);
  if (color_sensor_it != color_text_sensors_.end() && color_sensor_it->second) {
    color_sensor_it->second->publish_state(rgb_hex);
  }
  
  // Save to persistent storage (scheduler JSON)
  save_schedule_to_flash();
  ESP_LOGI(TAG, "Channel %u color updated to %s and saved", channel, rgb_hex.c_str());
}

void LEDBrickScheduler::set_channel_max_current(uint8_t channel, float max_current) {
  // Check if value actually changed
  float current_max = scheduler_.get_channel_max_current(channel);
  if (abs(current_max - max_current) < 0.01f) {
    return;  // No change, skip save
  }
  
  scheduler_.set_channel_max_current(channel, max_current);
  
  // Save to persistent storage (scheduler JSON)
  save_schedule_to_flash();
  ESP_LOGI(TAG, "Channel %u max current updated to %.2fA and saved", channel, max_current);
}

void LEDBrickScheduler::add_color_text_sensor(uint8_t channel, text_sensor::TextSensor *sensor) {
  color_text_sensors_[channel] = sensor;
  ESP_LOGD(TAG, "Added color text sensor for channel %u", channel);
}

void LEDBrickScheduler::update_color_sensors() {
  for (auto& pair : color_text_sensors_) {
    uint8_t channel = pair.first;
    text_sensor::TextSensor* sensor = pair.second;
    if (sensor) {
      std::string color = scheduler_.get_channel_color(channel);
      
      // Only update if color has changed
      auto last_it = last_colors_.find(channel);
      if (last_it == last_colors_.end() || last_it->second != color) {
        sensor->publish_state(color);
        last_colors_[channel] = color;
        ESP_LOGD(TAG, "Updated color sensor for channel %u: %s", channel, color.c_str());
      }
    }
  }
}

void LEDBrickScheduler::enable_moon_simulation(bool enabled) {
  // Check if value actually changed
  if (scheduler_.get_moon_simulation().enabled == enabled) {
    return;  // No change, skip save
  }
  
  scheduler_.enable_moon_simulation(enabled);
  
  // Save to persistent storage (scheduler JSON)
  save_schedule_to_flash();
  ESP_LOGI(TAG, "Moon simulation %s and saved", enabled ? "enabled" : "disabled");
}

void LEDBrickScheduler::set_moon_base_intensity(const std::vector<float>& intensity) {
  // Check if values actually changed
  auto current_moon = scheduler_.get_moon_simulation();
  if (current_moon.base_intensity.size() == intensity.size()) {
    bool changed = false;
    for (size_t i = 0; i < intensity.size(); i++) {
      if (abs(current_moon.base_intensity[i] - intensity[i]) > 0.01f) {
        changed = true;
        break;
      }
    }
    if (!changed) {
      return;  // No change, skip save
    }
  }
  
  scheduler_.set_moon_base_intensity(intensity);
  
  // Save to persistent storage (scheduler JSON)
  save_schedule_to_flash();
  ESP_LOGI(TAG, "Moon base intensity updated and saved");
}

void LEDBrickScheduler::set_moon_base_current(const std::vector<float>& current) {
  // Check if values actually changed
  auto current_moon = scheduler_.get_moon_simulation();
  if (current_moon.base_current.size() == current.size()) {
    bool changed = false;
    for (size_t i = 0; i < current.size(); i++) {
      if (abs(current_moon.base_current[i] - current[i]) > 0.01f) {
        changed = true;
        break;
      }
    }
    if (!changed) return;  // No change, skip save
  }
  
  scheduler_.set_moon_base_current(current);
  
  // Save to persistent storage (scheduler JSON)
  save_schedule_to_flash();
  ESP_LOGI(TAG, "Moon base current updated and saved");
}

void LEDBrickScheduler::set_moon_simulation(const LEDScheduler::MoonSimulation& config) {
  // Check if values actually changed  
  auto current_moon = scheduler_.get_moon_simulation();
  
  ESP_LOGD(TAG, "Current moon: enabled=%d, pwm_scale=%d, curr_scale=%d, min_curr=%.3f",
           current_moon.enabled, current_moon.phase_scaling_pwm, 
           current_moon.phase_scaling_current, current_moon.min_current_threshold);
  ESP_LOGD(TAG, "New moon: enabled=%d, pwm_scale=%d, curr_scale=%d, min_curr=%.3f",
           config.enabled, config.phase_scaling_pwm, 
           config.phase_scaling_current, config.min_current_threshold);
  if (current_moon.enabled == config.enabled && 
      current_moon.phase_scaling_pwm == config.phase_scaling_pwm &&
      current_moon.phase_scaling_current == config.phase_scaling_current &&
      abs(current_moon.min_current_threshold - config.min_current_threshold) < 0.001f &&
      current_moon.base_intensity.size() == config.base_intensity.size() &&
      current_moon.base_current.size() == config.base_current.size()) {
    bool changed = false;
    
    // Check intensity values
    for (size_t i = 0; i < config.base_intensity.size(); i++) {
      if (abs(current_moon.base_intensity[i] - config.base_intensity[i]) > 0.01f) {
        changed = true;
        break;
      }
    }
    
    // Check current values
    if (!changed) {
      for (size_t i = 0; i < config.base_current.size(); i++) {
        if (abs(current_moon.base_current[i] - config.base_current[i]) > 0.001f) {
          changed = true;
          break;
        }
      }
    }
    
    if (!changed) {
      return;  // No change, skip save
    }
  }
  
  scheduler_.set_moon_simulation(config);
  
  // Save to persistent storage (scheduler JSON)
  save_schedule_to_flash();
  ESP_LOGI(TAG, "Moon simulation configuration updated and saved");
}

void LEDBrickScheduler::update_astronomical_times_for_scheduler(bool force) {
  uint32_t current_millis = millis();
  
  // Update astronomical times every 5 minutes (300000 ms) unless forced
  if (!force && current_millis - last_astro_update_ms_ < 300000 && last_astro_update_ms_ != 0) {
    return; // Skip update if less than 5 minutes have passed
  }
  
  // Check if we have a valid time source
  if (!time_source_) {
    ESP_LOGW(TAG, "No time source available for astronomical calculations");
    return;
  }
  
  auto time = time_source_->now();
  if (!time.is_valid()) {
    ESP_LOGW(TAG, "Time not valid for astronomical calculations");
    return;
  }
  
  last_astro_update_ms_ = current_millis;
  
  // Calculate current astronomical times
  update_astro_calculator_settings();
  auto dt = esphome_time_to_datetime();
  
  // Get sunrise/sunset times (with projection if enabled)
  const auto &daily = get_daily_astro_times_();
  auto sun_times = daily.projected_sun;
  
  // Calculate solar noon (midpoint between sunrise and sunset)
  uint16_t solar_noon = 720; // Default noon
  if (sun_times.rise_valid && sun_times.set_valid) {
    // Handle case where sunset happens after midnight
    int rise_mins = static_cast<int>(sun_times.rise_minutes);
    int set_mins = static_cast<int>(sun_times.set_minutes);
    
    // If sunset is before sunrise, it means sunset is on the next day
    if (set_mins < rise_mins) {
      set_mins += 1440;  // Add 24 hours
    }
    
    solar_noon = (rise_mins + set_mins) / 2;
    
    // Wrap back to 0-1439 range
    while (solar_noon >= 1440) {
      solar_noon -= 1440;
    }
  }
  
  // Calculate civil twilight times (sun 6° below horizon)
  // For now, approximate as 30 minutes before/after sunrise/sunset
  uint16_t civil_dawn = sun_times.rise_valid ? 
    (sun_times.rise_minutes > 30 ? sun_times.rise_minutes - 30 : 0) : 390;
  uint16_t civil_dusk = sun_times.set_valid ? 
    (sun_times.set_minutes < 1410 ? sun_times.set_minutes + 30 : 1439) : 1110;
  
  // Build astronomical times structure
  LEDScheduler::AstronomicalTimes astro_times;
  astro_times.sunrise_minutes = sun_times.rise_valid ? sun_times.rise_minutes : 420;
  astro_times.sunset_minutes = sun_times.set_valid ? sun_times.set_minutes : 1080;
  astro_times.solar_noon_minutes = solar_noon;
  astro_times.civil_dawn_minutes = civil_dawn;
  astro_times.civil_dusk_minutes = civil_dusk;
  
  // For nautical and astronomical twilight, use further approximations
  astro_times.nautical_dawn_minutes = civil_dawn > 30 ? civil_dawn - 30 : 0;
  astro_times.nautical_dusk_minutes = civil_dusk < 1410 ? civil_dusk + 30 : 1439;
  astro_times.astronomical_dawn_minutes = civil_dawn > 60 ? civil_dawn - 60 : 0;
  astro_times.astronomical_dusk_minutes = civil_dusk < 1380 ? civil_dusk + 60 : 1439;
  
  // Get moon data (with projection if enabled)
  auto moon_times = daily.projected_moon;
  float moon_phase = astro_calc_.get_moon_phase(dt);
  
  astro_times.moonrise_minutes = moon_times.rise_valid ? moon_times.rise_minutes : 0;
  astro_times.moonset_minutes = moon_times.set_valid ? moon_times.set_minutes : 0;
  astro_times.moon_phase = moon_phase;
  astro_times.valid = true;
  
  // Update the scheduler with new astronomical times
  scheduler_.set_astronomical_times(astro_times);
  
  ESP_LOGD(TAG, "Updated astronomical times - Sunrise: %02u:%02u, Sunset: %02u:%02u, Solar Noon: %02u:%02u",
           astro_times.sunrise_minutes / 60, astro_times.sunrise_minutes % 60,
           astro_times.sunset_minutes / 60, astro_times.sunset_minutes % 60,
           astro_times.solar_noon_minutes / 60, astro_times.solar_noon_minutes % 60);
  
  if (moon_times.rise_valid || moon_times.set_valid) {
    ESP_LOGD(TAG, "Moon data - Rise: %02u:%02u, Set: %02u:%02u, %.0f%% lit (cycle %.2f)",
             astro_times.moonrise_minutes / 60, astro_times.moonrise_minutes % 60,
             astro_times.moonset_minutes / 60, astro_times.moonset_minutes % 60,
             AstronomicalCalculator::moon_illumination_from_phase(moon_phase) * 100.0f, moon_phase);
  }
}

LEDBrickScheduler::SchedulePointInfo LEDBrickScheduler::get_schedule_point_info(size_t index) const {
  SchedulePointInfo info;
  
  if (index >= scheduler_.get_schedule_size()) {
    info.time_type = "invalid";
    info.offset_minutes = 0;
    info.time_minutes = 0;
    return info;
  }
  
  // Get the raw schedule point data
  auto points = scheduler_.get_schedule_points();
  if (index >= points.size()) {
    info.time_type = "invalid";
    info.offset_minutes = 0;
    info.time_minutes = 0;
    return info;
  }
  
  const auto& point = points[index];
  
  // Convert time type enum to string
  switch (point.time_type) {
    case LEDScheduler::DynamicTimeType::FIXED:
      info.time_type = "fixed";
      break;
    case LEDScheduler::DynamicTimeType::SUNRISE_RELATIVE:
      info.time_type = "sunrise_relative";
      break;
    case LEDScheduler::DynamicTimeType::SUNSET_RELATIVE:
      info.time_type = "sunset_relative";
      break;
    case LEDScheduler::DynamicTimeType::SOLAR_NOON:
      info.time_type = "solar_noon";
      break;
    case LEDScheduler::DynamicTimeType::CIVIL_DAWN:
      info.time_type = "civil_dawn";
      break;
    case LEDScheduler::DynamicTimeType::CIVIL_DUSK:
      info.time_type = "civil_dusk";
      break;
    case LEDScheduler::DynamicTimeType::NAUTICAL_DAWN:
      info.time_type = "nautical_dawn";
      break;
    case LEDScheduler::DynamicTimeType::NAUTICAL_DUSK:
      info.time_type = "nautical_dusk";
      break;
    default:
      info.time_type = "unknown";
  }
  
  info.offset_minutes = point.offset_minutes;
  info.time_minutes = point.time_minutes;
  
  return info;
}

bool LEDBrickScheduler::set_channel_manual_control(uint8_t channel, float pwm, float current) {
  // Only allow manual control when scheduler is disabled
  if (enabled_) {
    ESP_LOGW(TAG, "Manual control rejected - scheduler is enabled");
    return false;
  }
  
  // Outputs stay off for the whole thermal emergency
  if (is_thermal_emergency()) {
    ESP_LOGW(TAG, "Manual control rejected - thermal emergency active");
    return false;
  }
  
  if (channel >= num_channels_) {
    ESP_LOGW(TAG, "Invalid channel %u for manual control", channel);
    return false;
  }
  
  ESP_LOGI(TAG, "Setting manual control for channel %u: PWM=%.1f%%, Current=%.2fA", 
           channel, pwm, current);
  
  // Set light brightness (PWM)
  auto light_it = lights_.find(channel);
  if (light_it != lights_.end() && light_it->second) {
    if (pwm <= 0.001f) {
      // Turn off light when PWM is 0
      auto call = light_it->second->turn_off();
      call.perform();
    } else {
      // Turn on and set brightness
      auto call = light_it->second->turn_on();
      call.set_brightness(pwm / 100.0f);  // Convert percentage to 0-1
      call.perform();
    }
  }
  
  // Set current control
  auto current_it = current_controls_.find(channel);
  if (current_it != current_controls_.end() && current_it->second) {
    // Apply max current limiting
    auto max_current_it = max_current_controls_.find(channel);
    if (max_current_it != max_current_controls_.end() && max_current_it->second) {
      float max_current = max_current_it->second->state;
      current = std::min(current, max_current);
    }
    current_it->second->publish_state(current);
  }
  return true;
}

void LEDBrickScheduler::set_thermal_emergency(bool emergency) {
  // Note: This method is now mostly deprecated since thermal emergency is managed by 
  // TemperatureHardwareManager. The actual state should be read from hardware state.
  ESP_LOGW(TAG, "set_thermal_emergency() called with emergency=%s - prefer using TemperatureControl system", 
           emergency ? "true" : "false");
  
  if (emergency) {
    ESP_LOGW(TAG, "MANUAL THERMAL EMERGENCY ACTIVATION - Forcing all channels to 0%%/0A");
    
    // Force all channels to zero PWM and current immediately
    for (uint8_t channel = 0; channel < num_channels_; channel++) {
      force_channel_output(channel, 0.0f, 0.0f);
    }
  } else {
    ESP_LOGI(TAG, "Manual thermal emergency clear request - Normal operation resumed");
  }
}

void LEDBrickScheduler::force_channel_output(uint8_t channel, float pwm, float current) {
  // Force specific PWM and current values regardless of schedule
  
  // Set light brightness using same method as apply_values for consistency
  auto light_it = lights_.find(channel);
  if (light_it != lights_.end() && light_it->second) {
    float brightness = pwm / 100.0f;  // Convert percentage to 0-1
    
    // Use make_call() to ensure consistent state management
    auto call = light_it->second->make_call();
    call.set_state(brightness > 0.001f); // Turn on if brightness > 0
    if (brightness > 0.001f) {
      call.set_brightness(brightness);
    }
    call.set_transition_length(0);  // No transition for immediate response
    call.perform();
    
    ESP_LOGV(TAG, "Force channel %u: PWM=%.1f%%, brightness=%.3f", channel, pwm, brightness);
  }
  
  // Set current control
  auto current_it = current_controls_.find(channel);
  if (current_it != current_controls_.end() && current_it->second) {
    current_it->second->publish_state(current);
  }
  
  ESP_LOGD(TAG, "Forced channel %u to PWM: %.1f%%, Current: %.2fA", channel, pwm, current);
}

void LEDBrickScheduler::add_temperature_sensor(const std::string &name, sensor::Sensor *sensor) {
  if (!sensor) {
    ESP_LOGW(TAG, "Cannot add null temperature sensor: %s", name.c_str());
    return;
  }
  
  register_temperature_sensor_(name, sensor);
  ESP_LOGD(TAG, "Added temperature sensor: %s", name.c_str());
}

void LEDBrickScheduler::register_temperature_sensor_(const std::string &name, sensor::Sensor *sensor) {
  for (const auto &existing : temp_sensors_) {
    if (existing.sensor == sensor) {
      return;  // Already registered; a second callback would double each reading
    }
  }
  temp_sensors_.push_back({name, sensor});
  temp_control_.add_temperature_sensor(name);
  
  // Stamp each reading when the sensor publishes it, so a sensor that stops
  // reporting times out instead of being re-stamped with its last value
  sensor->add_on_state_callback([this, name](float temp) { this->on_temperature_reading_(name, temp); });
  if (sensor->has_state()) {
    on_temperature_reading_(name, sensor->state);
  }
}

void LEDBrickScheduler::on_temperature_reading_(const std::string &name, float temp) {
  // Basic sanity check on temperature value; NaN fails it too. A noisy 1-Wire bus fails
  // some reads, so the controller holds the last good value through a few of these
  if (!(temp > -50.0f && temp < 150.0f)) {
    ESP_LOGD(TAG, "Invalid temperature reading from %s: %.1f°C", name.c_str(), temp);
    temp_control_.report_failed_reading(name, millis());
    return;
  }
  temp_control_.update_temperature_sensor(name, temp, millis());
}

void LEDBrickScheduler::enable_temperature_control(bool enabled) {
  temp_control_enable_requested_ = true;
  temp_control_.enable(enabled);
  ESP_LOGI(TAG, "Temperature control %s", enabled ? "enabled" : "disabled");
  
  // Update enable switch state
  if (temp_enable_switch_) {
    temp_enable_switch_->publish_state(enabled);
  }
}

bool LEDBrickScheduler::set_temperature_config_json(const std::string& json, std::string *error) {
  // New limits could clear the latched emergency without a real recovery
  if (is_thermal_emergency()) {
    if (error) *error = "cannot change temperature settings during a thermal emergency";
    return false;
  }
  if (!temp_control_.import_config_json(json, error)) {
    return false;
  }
  
  // Update our local config
  temp_config_ = temp_control_.get_config();
  
  // Save to flash with the schedule
  save_schedule_to_flash();
  
  return true;
}

void LEDBrickScheduler::update_temperature_sensors() {
  uint32_t now = millis();
  
  // Auto-discover temperature sensors if we don't have any yet
  if (temp_sensors_.empty() && (now - last_discovery_check_ms_ > 10000)) {  // Check every 10 seconds
    last_discovery_check_ms_ = now;
    ESP_LOGI(TAG, "Searching for temperature sensors...");
    
    // Only attempt auto-discovery after boot is complete
    if (!boot_complete_) {
      ESP_LOGD(TAG, "Skipping sensor discovery - boot not complete");
      return;
    }
    
    // Scan all sensors for temperature sensors (by unit of measurement)
    for (auto* sensor : App.get_sensors()) {
      std::string unit = sensor->get_unit_of_measurement_ref().str();
      std::string name = sensor->get_name().str();
      
      // Debug log all sensors with units to help troubleshoot
      ESP_LOGD(TAG, "Checking sensor '%s' with unit '%s'", name.c_str(), unit.c_str());
      
      if ((unit == "°C" || unit == "°F" || unit == "C" || unit == "F") && sensor->has_state()) {
        // Exclude template sensors that are used for temperature control monitoring
        if (name.find("Temperature Control") != std::string::npos || 
            name.find("Control Current") != std::string::npos ||
            name.find("Control Target") != std::string::npos ||
            name.find("Control Fan") != std::string::npos ||
            name.find("PID") != std::string::npos) {
          ESP_LOGD(TAG, "Skipping template sensor: %s", name.c_str());
          continue;
        }
        
        // Check if we already have this sensor
        bool found = false;
        for (const auto &existing : temp_sensors_) {
          if (existing.sensor == sensor) {
            found = true;
            break;
          }
        }
        
        if (!found) {
          register_temperature_sensor_(name, sensor);
          ESP_LOGI(TAG, "Auto-discovered temperature sensor: %s (%s)", name.c_str(), unit.c_str());
        }
      }
    }
  }
  // Readings reach the controller through the callbacks set in register_temperature_sensor_()
}

void LEDBrickScheduler::update_fan_speed() {
  if (fan_speed_sensor_ && fan_speed_sensor_->has_state()) {
    float rpm = fan_speed_sensor_->state;
    temp_hardware_.update_fan_rpm(rpm);
  }
}

void LEDBrickScheduler::publish_temp_sensor_values() {
  auto status = temp_control_.get_status();
  
  // Publish current temperature
  if (current_temp_sensor_ && status.current_temp_c > -50.0f) {
    current_temp_sensor_->publish_state(status.current_temp_c);
  }
  
  // Publish target temperature
  if (target_temp_sensor_) {
    target_temp_sensor_->publish_state(status.target_temp_c);
  }
  
  // Publish fan PWM
  if (fan_pwm_sensor_) {
    fan_pwm_sensor_->publish_state(status.hardware.fan_pwm_percent);
  }
  
  // Publish PID error
  if (pid_error_sensor_) {
    pid_error_sensor_->publish_state(status.pid_error);
  }
  
  // Publish PID output
  if (pid_output_sensor_) {
    pid_output_sensor_->publish_state(status.pid_output);
  }
  
  // Publish thermal emergency state
  if (thermal_emergency_sensor_) {
    thermal_emergency_sensor_->publish_state(status.hardware.thermal_emergency);
  }
  
  // Publish fan enabled state
  if (fan_enabled_sensor_) {
    fan_enabled_sensor_->publish_state(status.hardware.fan_enabled);
  }
  
  // Update target temperature number control if value changed
  if (target_temp_number_ && 
      abs(target_temp_number_->state - status.target_temp_c) > 0.1f) {
    target_temp_number_->publish_state(status.target_temp_c);
  }
  
  // Update enable switch if needed
  if (temp_enable_switch_ && temp_enable_switch_->state != status.enabled) {
    temp_enable_switch_->publish_state(status.enabled);
  }
}

void LEDBrickScheduler::on_fan_pwm_change(float pwm) {
  ESP_LOGD(TAG, "Setting fan PWM to %.1f%%", pwm);
  
  if (fan_) {
    ESP_LOGI(TAG, "Fan object exists, setting PWM to %.1f%%", pwm);
    if (pwm <= 0.001f) {
      // Turn off fan when PWM is 0
      ESP_LOGI(TAG, "Turning fan OFF");
      auto call = fan_->turn_off();
      call.perform();
    } else {
      // Turn on fan and set speed
      ESP_LOGI(TAG, "Turning fan ON with speed %.1f", pwm);
      auto call = fan_->turn_on();
      call.set_speed(pwm);  // ESPHome fan expects speed in range 0-100
      call.perform();
    }
  } else {
    ESP_LOGW(TAG, "Fan object is NULL - cannot control fan!");
  }
}

void LEDBrickScheduler::on_fan_enable_change(bool enabled) {
  ESP_LOGD(TAG, "Setting fan power to %s", enabled ? "ON" : "OFF");
  
  if (fan_power_switch_) {
    if (enabled) {
      fan_power_switch_->turn_on();
    } else {
      fan_power_switch_->turn_off();
    }
  }
  
  // Also ensure fan is off when power is disabled
  if (!enabled && fan_) {
    auto call = fan_->turn_off();
    call.perform();
  }
}

void LEDBrickScheduler::on_emergency_change(bool emergency) {
  if (emergency) {
    ESP_LOGW(TAG, "THERMAL EMERGENCY ACTIVATED!");
    
    // Force all channels to zero immediately
    for (uint8_t channel = 0; channel < num_channels_; channel++) {
      force_channel_output(channel, 0.0f, 0.0f);
    }
  } else {
    ESP_LOGI(TAG, "Thermal emergency cleared - restoring normal operation");
    
    // Force the next update to apply all values
    force_next_update_ = true;
    
    // Immediately restore normal operation if scheduler is enabled and the clock is set
    if (enabled_ && has_valid_time()) {
      // Get current values and apply them
      uint16_t current_time = get_current_time_minutes();
      auto values = scheduler_.get_values_at_seconds_with_astro(get_current_time_seconds(), scheduler_.get_astronomical_times());
      
      if (values.valid) {
        ESP_LOGI(TAG, "Restoring scheduled values at %02d:%02d", current_time / 60, current_time % 60);
        // Log the values we're trying to restore
        for (size_t i = 0; i < values.pwm_values.size() && i < 3; i++) {
          ESP_LOGI(TAG, "  Channel %d: PWM=%.1f%%, Current=%.3fA", 
                   i, values.pwm_values[i], values.current_values[i]);
        }
        apply_values(values);
      }
    }
  }
  
  // Update emergency sensor
  if (thermal_emergency_sensor_) {
    thermal_emergency_sensor_->publish_state(emergency);
  }
  
  // Write the latch to flash now rather than at the next periodic sync, so a power
  // cut straight after an emergency still comes back with the LEDs off
  emergency_pref_.save(&emergency);
  global_preferences->sync();
}

bool LEDBrickScheduler::reset_thermal_emergency() {
  if (!is_thermal_emergency()) {
    return true;
  }
  // For a latch that cannot clear itself, such as a failed sensor. While a working sensor
  // still reads above the recovery temperature, keep the LEDs off.
  if (!temp_control_.emergency_reset_allowed()) {
    ESP_LOGW(TAG, "Thermal emergency reset refused: a sensor reads %.1f°C, above recovery",
             temp_control_.get_status().max_temp_c);
    return false;
  }
  ESP_LOGW(TAG, "Thermal emergency reset by user");
  ledbrick::TemperatureControlCommand command;
  command.fan_enabled = true;
  command.fan_pwm_percent = 100.0f;
  command.emergency_state = false;
  command.override_normal_control = true;
  command.reason = "Thermal emergency reset by user";
  temp_hardware_.apply_command(command, millis());
  temp_control_.update_hardware_state(temp_hardware_.get_hardware_state());
  return true;
}

} // namespace ledbrick_scheduler
} // namespace esphome
