theatrus/ledbrick/ledbrick-classic/firmware/nordic_nrf51/app/bsp/pca10028.h

/* Copyright (c) 2014 Nordic Semiconductor. All Rights Reserved.
 *
 * The information contained herein is property of Nordic Semiconductor ASA.
 * Terms and conditions of usage are described in detail in NORDIC
 * SEMICONDUCTOR STANDARD SOFTWARE LICENSE AGREEMENT.
 *
 * Licensees are granted free, non-transferable use of the information. NO
 * WARRANTY of ANY KIND is provided. This heading must NOT be removed from
 * the file.
 *
 */
#ifndef PCA10028_H
#define PCA10028_H

// LEDs definitions for PCA10028
#define LEDS_NUMBER    3

#define LED_START      10
#define LED_1          10
#define LED_2          11
#define LED_3          12
#define LED_STOP       12

#define LEDS_LIST { LED_1, LED_2, LED_3 }

#define BSP_LED_0      LED_1
#define BSP_LED_1      LED_2
#define BSP_LED_2      LED_3

#define BSP_LED_0_MASK (1<<BSP_LED_0)
#define BSP_LED_1_MASK (1<<BSP_LED_1)
#define BSP_LED_2_MASK (1<<BSP_LED_2)

#define LEDS_MASK      (BSP_LED_0_MASK | BSP_LED_1_MASK | BSP_LED_2_MASK)
/* all LEDs are lit when GPIO is low */
#define LEDS_INV_MASK  LEDS_MASK

#define BUTTONS_NUMBER 3

#define BUTTON_START   17
#define BUTTON_1       17
#define BUTTON_2       19
#define BUTTON_3       20
#define BUTTON_STOP    20
#define BUTTON_PULL    NRF_GPIO_PIN_PULLUP

#define BUTTONS_LIST { BUTTON_1, BUTTON_2, BUTTON_3 }

#define BSP_BUTTON_0   BUTTON_1
#define BSP_BUTTON_1   BUTTON_2
#define BSP_BUTTON_2   BUTTON_3


#define BSP_BUTTON_0_MASK (1<<BSP_BUTTON_0)
#define BSP_BUTTON_1_MASK (1<<BSP_BUTTON_1)
#define BSP_BUTTON_2_MASK (1<<BSP_BUTTON_2)

#define BUTTONS_MASK   0x001a0000



#endif // PCA10028_H
