theatrus/ledbrick/firmware/test_scheduler.cpp

#include "components/ledbrick_scheduler/scheduler.h"
#include "test_framework.h"
#include <iostream>
#include <iomanip>
#include <cassert>
#include <cmath>

void test_basic_functionality(TestRunner& runner) {
    runner.start_suite("Basic Functionality Tests");
    
    LEDScheduler scheduler(4);
    
    // Test initial state
    runner.assert_equals(4, static_cast<int>(scheduler.get_num_channels()), "Initial channel count");
    runner.assert_true(scheduler.is_schedule_empty(), "Initial schedule is empty");
    runner.assert_equals(0, static_cast<int>(scheduler.get_schedule_size()), "Initial schedule size");
    
    // Test adding a schedule point
    std::vector<float> pwm_values = {50.0f, 60.0f, 70.0f, 80.0f};
    std::vector<float> current_values = {1.0f, 1.2f, 1.4f, 1.6f};
    scheduler.set_schedule_point(720, pwm_values, current_values); // 12:00 PM
    
    runner.assert_false(scheduler.is_schedule_empty(), "Schedule not empty after adding point");
    runner.assert_equals(1, static_cast<int>(scheduler.get_schedule_size()), "Schedule size after adding point");
    
    // Test getting values at the exact time
    auto result = scheduler.get_values_at_time(720);
    runner.assert_true(result.valid, "Result valid at exact time");
    runner.assert_equals(50.0f, result.pwm_values[0], 0.01f, "PWM value at exact time (expected: 50.0, actual: " + std::to_string(result.pwm_values[0]) + ")");
    runner.assert_equals(1.6f, result.current_values[3], 0.01f, "Current value at exact time (expected: 1.6, actual: " + std::to_string(result.current_values[3]) + ")");
}

void test_interpolation(TestRunner& runner) {
    runner.start_suite("Interpolation Tests");
    
    LEDScheduler scheduler(2);
    
    // Add two schedule points
    scheduler.set_schedule_point(480, {20.0f, 30.0f}, {0.4f, 0.6f}); // 8:00 AM
    scheduler.set_schedule_point(1200, {80.0f, 90.0f}, {1.6f, 1.8f}); // 8:00 PM
    
    // Test interpolation at midpoint
    auto result = scheduler.get_values_at_time(840); // 2:00 PM (midpoint)
    runner.assert_true(result.valid, "Interpolation result valid");
    runner.assert_equals(50.0f, result.pwm_values[0], 1.0f, "PWM interpolated value channel 0 (expected: 50.0, actual: " + std::to_string(result.pwm_values[0]) + ")");
    runner.assert_equals(60.0f, result.pwm_values[1], 1.0f, "PWM interpolated value channel 1 (expected: 60.0, actual: " + std::to_string(result.pwm_values[1]) + ")");
    runner.assert_equals(1.0f, result.current_values[0], 0.1f, "Current interpolated value channel 0 (expected: 1.0, actual: " + std::to_string(result.current_values[0]) + ")");
    runner.assert_equals(1.2f, result.current_values[1], 0.1f, "Current interpolated value channel 1 (expected: 1.2, actual: " + std::to_string(result.current_values[1]) + ")");
}

void test_presets(TestRunner& runner) {
    runner.start_suite("Preset Tests");
    
    LEDScheduler scheduler(4);
    
    // Test default preset
    scheduler.load_preset("default");
    runner.assert_false(scheduler.is_schedule_empty(), "Default preset loaded");
    runner.assert_true(scheduler.get_schedule_size() > 0, "Preset has schedule points");
    
    // Also test with legacy name
    scheduler.clear_schedule();
    scheduler.load_preset("sunrise_sunset");
    runner.assert_false(scheduler.is_schedule_empty(), "Legacy preset name still works");
    
    // Test that preset names only returns default
    auto preset_names = scheduler.get_preset_names();
    runner.assert_equals(1, static_cast<int>(preset_names.size()), "Only one preset available");
    runner.assert_true(preset_names[0] == "default", "Default preset name returned");

    // An unknown preset is reported and leaves the schedule alone
    size_t loaded_size = scheduler.get_schedule_size();
    runner.assert_true(scheduler.load_preset("default"), "Known preset reports success");
    runner.assert_false(scheduler.load_preset("no_such_preset"), "Unknown preset reports failure");
    runner.assert_equals(static_cast<int>(loaded_size), static_cast<int>(scheduler.get_schedule_size()),
                         "Unknown preset leaves schedule unchanged");

    // A preset kept with save_preset loads back
    scheduler.clear_schedule();
    scheduler.add_schedule_point(LEDScheduler::SchedulePoint(600, {10.0f, 20.0f, 30.0f, 40.0f}, {0.5f, 0.5f, 0.5f, 0.5f}));
    scheduler.save_preset("mine");
    scheduler.load_preset("default");
    runner.assert_true(scheduler.load_preset("mine"), "Saved preset loads");
    runner.assert_equals(1, static_cast<int>(scheduler.get_schedule_size()), "Saved preset restores its points");
}

void test_serialization(TestRunner& runner) {
    runner.start_suite("Serialization Tests");
    
    LEDScheduler scheduler1(3);
    scheduler1.set_schedule_point(360, {10.0f, 20.0f, 30.0f}, {0.2f, 0.4f, 0.6f}); // 6:00 AM
    scheduler1.set_schedule_point(1080, {40.0f, 50.0f, 60.0f}, {0.8f, 1.0f, 1.2f}); // 6:00 PM
    
    // Serialize
    auto serialized = scheduler1.serialize();
    runner.assert_equals(2, static_cast<int>(serialized.num_points), "Serialized point count");
    runner.assert_equals(3, static_cast<int>(serialized.num_channels), "Serialized channel count");
    runner.assert_true(serialized.data.size() > 0, "Serialized data not empty");
    
    // Deserialize to new scheduler
    LEDScheduler scheduler2(1); // Different initial channel count
    bool deserialized = scheduler2.deserialize(serialized);
    runner.assert_true(deserialized, "Deserialization successful");
    runner.assert_equals(3, static_cast<int>(scheduler2.get_num_channels()), "Deserialized channel count");
    runner.assert_equals(2, static_cast<int>(scheduler2.get_schedule_size()), "Deserialized schedule size");
    
    // Verify values
    auto result = scheduler2.get_values_at_time(360);
    runner.assert_true(result.valid, "Deserialized values valid");
    runner.assert_equals(10.0f, result.pwm_values[0], 0.01f, "Deserialized PWM value (expected: 10.0, actual: " + std::to_string(result.pwm_values[0]) + ")");
    runner.assert_equals(0.2f, result.current_values[0], 0.01f, "Deserialized current ch0 (expected: 0.2, actual: " + std::to_string(result.current_values[0]) + ")");
    runner.assert_equals(0.4f, result.current_values[1], 0.01f, "Deserialized current ch1 (expected: 0.4, actual: " + std::to_string(result.current_values[1]) + ")");
    runner.assert_equals(0.6f, result.current_values[2], 0.01f, "Deserialized current ch2 (expected: 0.6, actual: " + std::to_string(result.current_values[2]) + ")");
}

void test_json_export(TestRunner& runner) {
    runner.start_suite("JSON Export Tests");
    
    LEDScheduler scheduler(2);
    scheduler.set_schedule_point(720, {75.0f, 85.0f}, {1.5f, 1.7f}); // 12:00 PM
    
    std::string json = scheduler.export_json();
    runner.assert_true(json.length() > 50, "JSON export not empty");
    runner.assert_true(json.find("\"num_channels\":") != std::string::npos && json.find("2") != std::string::npos, "JSON contains channel count");
    runner.assert_true(json.find("\"time_minutes\":") != std::string::npos && json.find("720") != std::string::npos, "JSON contains time");
    runner.assert_true(json.find("75") != std::string::npos, "JSON contains PWM value");
    runner.assert_true(json.find("1.7") != std::string::npos, "JSON contains current value");
    runner.assert_true(json.find("1.7000000476837158") == std::string::npos, "JSON numbers are rounded");
    
    std::cout << "Sample JSON export:\n" << json.substr(0, 200) << "..." << std::endl;
}

void test_json_import(TestRunner& runner) {
    runner.start_suite("JSON Import Tests");
    
    // Test 1: Import a simple fixed schedule
    LEDScheduler scheduler(2);
    std::string json_fixed = R"({
        "num_channels": 2,
        "schedule_points": [
            {
                "time_type": "fixed",
                "time_minutes": 360,
                "pwm_values": [50.0, 60.0],
                "current_values": [1.0, 1.2]
            },
            {
                "time_type": "fixed", 
                "time_minutes": 720,
                "pwm_values": [80.0, 90.0],
                "current_values": [1.6, 1.8]
            }
        ]
    })";
    
    bool success = scheduler.import_json(json_fixed);
    runner.assert_true(success, "Import fixed schedule succeeded");
    runner.assert_equals(2, static_cast<int>(scheduler.get_schedule_size()), "Imported 2 fixed points");
    
    // Verify imported values
    auto result = scheduler.get_values_at_time(360);
    runner.assert_equals(50.0f, result.pwm_values[0], 0.01f, "Imported PWM ch1 at 6 AM");
    runner.assert_equals(60.0f, result.pwm_values[1], 0.01f, "Imported PWM ch2 at 6 AM");
    runner.assert_equals(1.0f, result.current_values[0], 0.01f, "Imported current ch1 at 6 AM");
    
    // Test 2: Import dynamic schedule
    scheduler.clear_schedule();
    std::string json_dynamic = R"({
        "num_channels": 2,
        "schedule_points": [
            {
                "time_type": "sunrise_relative",
                "offset_minutes": -30,
                "time_minutes": 0,
                "pwm_values": [10.0, 15.0],
                "current_values": [0.2, 0.3]
            },
            {
                "time_type": "sunset_relative",
                "offset_minutes": 60,
                "time_minutes": 0,
                "pwm_values": [5.0, 7.0],
                "current_values": [0.1, 0.14]
            }
        ]
    })";
    
    success = scheduler.import_json(json_dynamic);
    runner.assert_true(success, "Import dynamic schedule succeeded");
    runner.assert_equals(2, static_cast<int>(scheduler.get_schedule_size()), "Imported 2 dynamic points");
    
    // Test 3: Import empty schedule
    scheduler.set_schedule_point(720, {50.0f, 50.0f}, {1.0f, 1.0f}); // Add a point first
    size_t size_before_empty_import = scheduler.get_schedule_size();
    std::string json_empty = R"({
        "num_channels": 2,
        "schedule_points": []
    })";
    
    success = scheduler.import_json(json_empty);
    runner.assert_false(success, "Import empty schedule returns false");
    runner.assert_equals(static_cast<int>(size_before_empty_import), static_cast<int>(scheduler.get_schedule_size()),
                         "Schedule unchanged on failed import");
    
    // Test 4: Import invalid JSON
    std::string json_invalid = "{ invalid json ]";
    success = scheduler.import_json(json_invalid);
    runner.assert_false(success, "Import invalid JSON returns false");
    
    // Test 5: Import with channel count change
    scheduler.set_num_channels(2);
    std::string json_channels = R"({
        "num_channels": 4,
        "schedule_points": [
            {
                "time_type": "fixed",
                "time_minutes": 600,
                "pwm_values": [30.0, 40.0, 50.0, 60.0],
                "current_values": [0.6, 0.8, 1.0, 1.2]
            }
        ]
    })";
    
    success = scheduler.import_json(json_channels);
    runner.assert_true(success, "Import with channel count change succeeded");
    runner.assert_equals(4, static_cast<int>(scheduler.get_num_channels()), "Channel count updated");
    
    auto ch_result = scheduler.get_values_at_time(600);
    runner.assert_equals(4, static_cast<int>(ch_result.pwm_values.size()), "Result has 4 channels");
    runner.assert_equals(50.0f, ch_result.pwm_values[2], 0.01f, "Channel 3 PWM value correct");
    
    // Test 6: Round-trip export/import
    LEDScheduler scheduler_export(3);
    scheduler_export.add_dynamic_schedule_point(LEDScheduler::DynamicTimeType::SOLAR_NOON, 0,
        {70.0f, 80.0f, 90.0f}, {1.4f, 1.6f, 1.8f});
    scheduler_export.set_schedule_point(480, {20.0f, 25.0f, 30.0f}, {0.4f, 0.5f, 0.6f});
    
    std::string exported = scheduler_export.export_json();
    
    LEDScheduler scheduler_import(1); // Start with different channel count
    success = scheduler_import.import_json(exported);
    runner.assert_true(success, "Round-trip import succeeded");
    runner.assert_equals(3, static_cast<int>(scheduler_import.get_num_channels()), "Channel count restored");
    runner.assert_equals(2, static_cast<int>(scheduler_import.get_schedule_size()), "Schedule size preserved");
}

void test_edge_cases(TestRunner& runner) {
    runner.start_suite("Edge Case Tests");
    
    LEDScheduler scheduler(2);
    
    // Test invalid time values
    auto result = scheduler.get_values_at_time(1440); // Invalid: >= 1440
    runner.assert_false(result.valid, "Invalid time rejected");
    
    result = scheduler.get_values_at_time(1500); // Invalid: > 1440
    runner.assert_false(result.valid, "Invalid time rejected");
    
    // Test empty schedule
    result = scheduler.get_values_at_time(720);
    runner.assert_false(result.valid, "Empty schedule returns invalid");
    
    // Test single point schedule
    scheduler.set_schedule_point(600, {50.0f, 60.0f}, {1.0f, 1.2f});
    result = scheduler.get_values_at_time(300); // Before point
    runner.assert_true(result.valid, "Single point interpolation valid");
    
    result = scheduler.get_values_at_time(900); // After point
    runner.assert_true(result.valid, "Single point interpolation valid");
    
    // Test boundary conditions
    result = scheduler.get_values_at_time(0); // Midnight
    runner.assert_true(result.valid, "Midnight interpolation valid");
    
    result = scheduler.get_values_at_time(1439); // 23:59
    runner.assert_true(result.valid, "End of day interpolation valid");
}

void test_channel_management(TestRunner& runner) {
    runner.start_suite("Channel Management Tests");
    
    LEDScheduler scheduler(2);
    scheduler.set_schedule_point(720, {50.0f, 60.0f}, {1.0f, 1.2f});
    
    // Test channel count change
    scheduler.set_num_channels(4);
    runner.assert_equals(4, static_cast<int>(scheduler.get_num_channels()), "Channel count updated");
    
    auto result = scheduler.get_values_at_time(720);
    runner.assert_true(result.valid, "Schedule valid after channel change");
    runner.assert_equals(4, static_cast<int>(result.pwm_values.size()), "PWM values resized");
    runner.assert_equals(4, static_cast<int>(result.current_values.size()), "Current values resized");
    
    // Original values should be preserved
    runner.assert_equals(50.0f, result.pwm_values[0], 0.01f, "Original PWM preserved channel 0 (expected: 50.0, actual: " + std::to_string(result.pwm_values[0]) + ")");
    runner.assert_equals(60.0f, result.pwm_values[1], 0.01f, "Original PWM preserved channel 1 (expected: 60.0, actual: " + std::to_string(result.pwm_values[1]) + ")");
    runner.assert_equals(0.0f, result.pwm_values[2], 0.01f, "New PWM defaulted to 0 channel 2 (expected: 0.0, actual: " + std::to_string(result.pwm_values[2]) + ")");
    runner.assert_equals(0.0f, result.pwm_values[3], 0.01f, "New PWM defaulted to 0 channel 3 (expected: 0.0, actual: " + std::to_string(result.pwm_values[3]) + ")");
}

void test_mutations(TestRunner& runner) {
    runner.start_suite("Schedule Mutation Tests");
    
    LEDScheduler scheduler(2);
    
    // Add multiple points
    scheduler.set_schedule_point(480, {20.0f, 30.0f}, {0.4f, 0.6f}); // 8:00 AM
    scheduler.set_schedule_point(720, {50.0f, 60.0f}, {1.0f, 1.2f}); // 12:00 PM
    scheduler.set_schedule_point(1200, {80.0f, 90.0f}, {1.6f, 1.8f}); // 8:00 PM
    
    runner.assert_equals(3, static_cast<int>(scheduler.get_schedule_size()), "Three points added");
    
    // Update existing point (same time)
    scheduler.set_schedule_point(720, {55.0f, 65.0f}, {1.1f, 1.3f}); // Updated 12:00 PM
    runner.assert_equals(3, static_cast<int>(scheduler.get_schedule_size()), "Size unchanged after update");
    
    auto result = scheduler.get_values_at_time(720);
    runner.assert_equals(55.0f, result.pwm_values[0], 0.01f, "Point updated correctly (expected: 55.0, actual: " + std::to_string(result.pwm_values[0]) + ")");
    
    // Remove point
    scheduler.remove_schedule_point(720);
    runner.assert_equals(2, static_cast<int>(scheduler.get_schedule_size()), "Point removed");
    
    // Clear schedule
    scheduler.clear_schedule();
    runner.assert_equals(0, static_cast<int>(scheduler.get_schedule_size()), "Schedule cleared");
    runner.assert_true(scheduler.is_schedule_empty(), "Schedule is empty after clear");
}

void test_dynamic_schedule_points(TestRunner& runner) {
    runner.start_suite("Dynamic Schedule Point Tests");
    
    LEDScheduler scheduler(2);
    
    // Test adding dynamic schedule points
    scheduler.add_dynamic_schedule_point(LEDScheduler::DynamicTimeType::SUNRISE_RELATIVE, -30,
        std::vector<float>{10.0f, 20.0f}, std::vector<float>{0.2f, 0.4f});
    scheduler.add_dynamic_schedule_point(LEDScheduler::DynamicTimeType::SOLAR_NOON, 0,
        std::vector<float>{80.0f, 90.0f}, std::vector<float>{1.6f, 1.8f});
    scheduler.add_dynamic_schedule_point(LEDScheduler::DynamicTimeType::SUNSET_RELATIVE, 30,
        std::vector<float>{15.0f, 25.0f}, std::vector<float>{0.3f, 0.5f});
    
    runner.assert_equals(3, static_cast<int>(scheduler.get_schedule_size()), "Dynamic points added");
    
    // Test dynamic time calculation
    LEDScheduler::AstronomicalTimes astro_times;
    astro_times.sunrise_minutes = 420;  // 7:00 AM
    astro_times.sunset_minutes = 1080;  // 6:00 PM
    astro_times.solar_noon_minutes = 750; // 12:30 PM
    astro_times.valid = true;
    
    auto points = scheduler.get_schedule_points();
    
    // Test sunrise relative calculation
    uint16_t sunrise_time = scheduler.calculate_dynamic_time(points[0], astro_times);
    runner.assert_equals(390, static_cast<int>(sunrise_time), "Sunrise -30 minutes = 6:30 AM");
    
    // Test solar noon calculation
    uint16_t noon_time = scheduler.calculate_dynamic_time(points[1], astro_times);
    runner.assert_equals(750, static_cast<int>(noon_time), "Solar noon = 12:30 PM");
    
    // Test sunset relative calculation
    uint16_t sunset_time = scheduler.calculate_dynamic_time(points[2], astro_times);
    runner.assert_equals(1110, static_cast<int>(sunset_time), "Sunset +30 minutes = 6:30 PM");
    
    // Test interpolation with astronomical times
    auto result = scheduler.get_values_at_time_with_astro(750, astro_times);
    runner.assert_true(result.valid, "Dynamic interpolation valid");
    runner.assert_equals(80.0f, result.pwm_values[0], 1.0f, "Dynamic PWM value at solar noon (expected: 80.0, actual: " + std::to_string(result.pwm_values[0]) + ")");
    
    // Test default preset (which is now dynamic)
    scheduler.load_preset("default");
    runner.assert_equals(5, static_cast<int>(scheduler.get_schedule_size()), "Default preset loaded");
    
    // Test JSON export includes dynamic info
    std::string json = scheduler.export_json();
    runner.assert_true(json.find("\"time_type\":") != std::string::npos && json.find("\"sunrise_relative\"") != std::string::npos, 
                      "JSON contains dynamic type info");
}
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
