theatrus/ledbrick/firmware/test_temperature_control.cpp

#include "components/ledbrick_scheduler/temperature_control.h"
#include "test_framework.h"
#include <cmath>
#include <vector>

using namespace ledbrick;

// Test helper to simulate the new architecture
class TemperatureControlTestHelper {
public:
    TemperatureControl controller;
    TemperatureHardwareManager hardware;
    
    TemperatureControlTestHelper() {
        // Don't enable by default - let tests control this
    }
    
    void update(uint32_t current_time_ms) {
        auto command = controller.compute_control_command(current_time_ms);
        hardware.apply_command(command, current_time_ms);
        controller.update_hardware_state(hardware.get_hardware_state());
    }
    
    const TemperatureControlStatus& get_status() {
        return controller.get_status();
    }
};

void test_sensor_management(TestRunner& runner) {
    runner.start_suite("Sensor Management Tests");
    
    TemperatureControlTestHelper helper;
    helper.controller.enable(true); // Enable to allow updates
    
    // Add sensors
    helper.controller.add_temperature_sensor("sensor1");
    helper.controller.add_temperature_sensor("sensor2");
    helper.controller.add_temperature_sensor("sensor3");
    
    // Verify sensor count through status
    helper.update(1000);
    auto status = helper.get_status();
    runner.assert_equals(3, static_cast<int>(status.sensors_total_count), "Total sensor count");
    
    // All sensors invalid initially
    runner.assert_equals(0, static_cast<int>(status.sensors_valid_count), "Valid sensor count (no data)");
}

void test_sensor_validity(TestRunner& runner) {
    runner.start_suite("Sensor Validity Tests");
    
    TemperatureControlTestHelper helper;
    helper.controller.enable(true); // Enable to allow updates
    TemperatureControlConfig config;
    config.sensor_timeout_ms = 5000; // 5 second timeout
    helper.controller.set_config(config);
    
    helper.controller.add_temperature_sensor("sensor1");
    helper.controller.add_temperature_sensor("sensor2");
    
    // Update sensors
    helper.controller.update_temperature_sensor("sensor1", 25.0f, 1000);
    helper.controller.update_temperature_sensor("sensor2", 26.0f, 1000);
    
    helper.update(1500); // 500ms later
    auto status = helper.get_status();
    runner.assert_equals(2, static_cast<int>(status.sensors_valid_count), "Both sensors valid");
    
    // Fast forward past timeout for sensor2
    helper.update(7000); // 6 seconds later
    status = helper.get_status();
    runner.assert_equals(0, static_cast<int>(status.sensors_valid_count), "Both sensors timed out");
    
    // Update one sensor
    helper.controller.update_temperature_sensor("sensor1", 25.5f, 7000);
    helper.update(7100);
    status = helper.get_status();
    runner.assert_equals(1, static_cast<int>(status.sensors_valid_count), "One sensor valid");
}

void test_temperature_averaging(TestRunner& runner) {
    runner.start_suite("Temperature Averaging Tests");
    
    TemperatureControlTestHelper helper;
    helper.controller.enable(true); // Enable to allow updates
    
    // Disable filtering for accurate averaging tests
    TemperatureControlConfig config;
    config.temp_filter_alpha = 1.0f; // No filtering
    helper.controller.set_config(config);
    
    helper.controller.add_temperature_sensor("sensor1");
    helper.controller.add_temperature_sensor("sensor2");
    helper.controller.add_temperature_sensor("sensor3");
    
    // Update with different temperatures
    helper.controller.update_temperature_sensor("sensor1", 25.0f, 1000);
    helper.controller.update_temperature_sensor("sensor2", 27.0f, 1000);
    helper.controller.update_temperature_sensor("sensor3", 26.0f, 1000);
    
    helper.update(1100);
    auto status = helper.get_status();
    
    // Average should be (25 + 27 + 26) / 3 = 26
    runner.assert_equals(26.0f, status.current_temp_c, 0.001f, "Average temperature");
    
    // Test with one invalid sensor
    // Wait for sensor3 to timeout (it was last updated at time 1000)
    helper.update(12000); // More than 10s after sensor3's last update
    
    // Update only sensor1 and sensor2
    helper.controller.update_temperature_sensor("sensor1", 30.0f, 12000);
    helper.controller.update_temperature_sensor("sensor2", 32.0f, 12000);
    // sensor3 remains timed out
    
    helper.update(12100);
    status = helper.get_status();
    
    // Should average only the two valid sensors: (30 + 32) / 2 = 31
    runner.assert_equals(31.0f, status.current_temp_c, 0.001f, "Average with invalid sensor");
}
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
